basnetsaroj/Batch_distillation_paper/CAD Model/Traditional/Trad photos/Traditional assembled.png

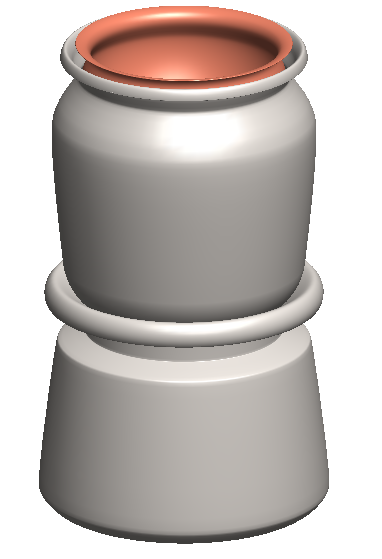
CAD Model/Traditional/Trad photos/Traditional assembled.png
