basnetsaroj/Batch_distillation_paper/CAD Model/CAD/Design Photos/Base container.png

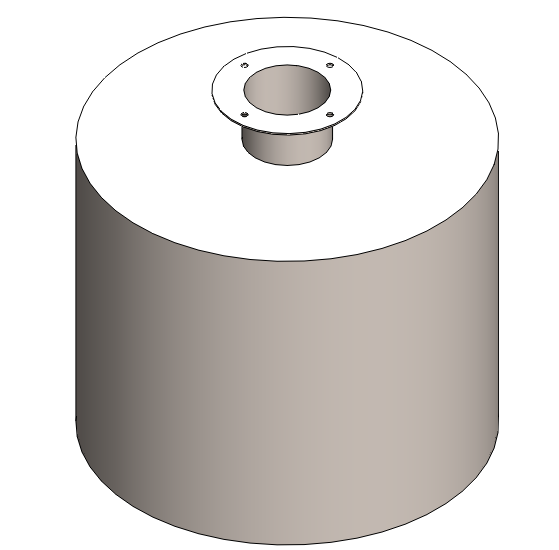
CAD Model/CAD/Design Photos/Base container.png
