basnetsaroj/Batch_distillation_paper/CAD Model/CAD/Design Photos/Column.png

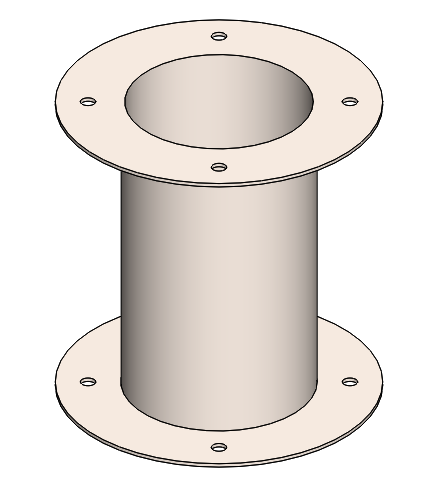
CAD Model/CAD/Design Photos/Column.png
