basnetsaroj/Batch_distillation_paper/CAD Model/CAD/Design Photos/condenser 2.PNG

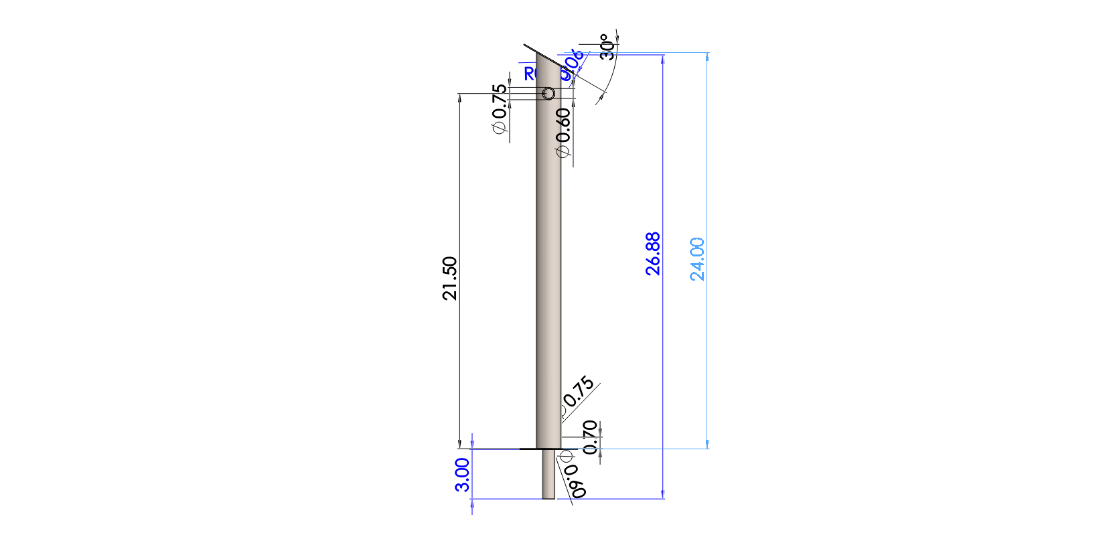
CAD Model/CAD/Design Photos/condenser 2.PNG
