basnetsaroj/Batch_distillation_paper/CAD Model/CAD/Design Photos/Condensor.PNG

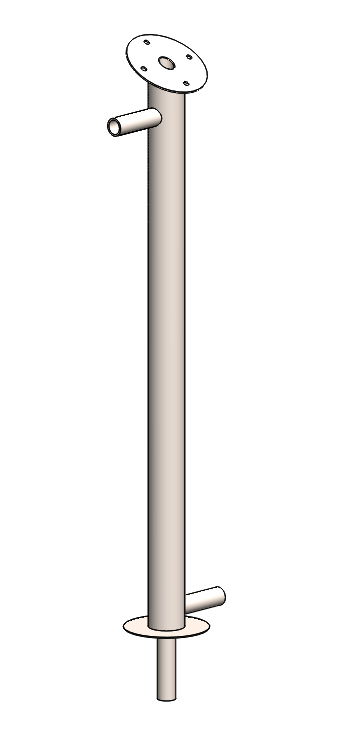
CAD Model/CAD/Design Photos/Condensor.PNG
