basnetsaroj/Batch_distillation_paper/CAD Model/CAD/Design Photos/dc.png

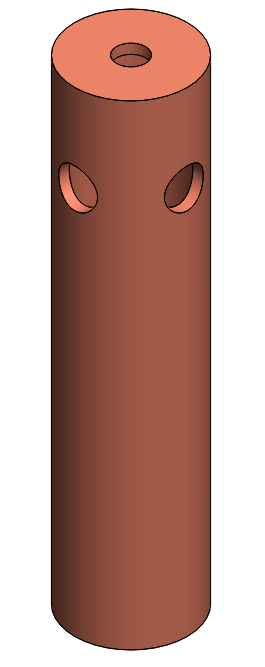
CAD Model/CAD/Design Photos/dc.png
