basnetsaroj/Batch_distillation_paper/CAD Model/CAD/Design Photos/Exploded Section of tray.png

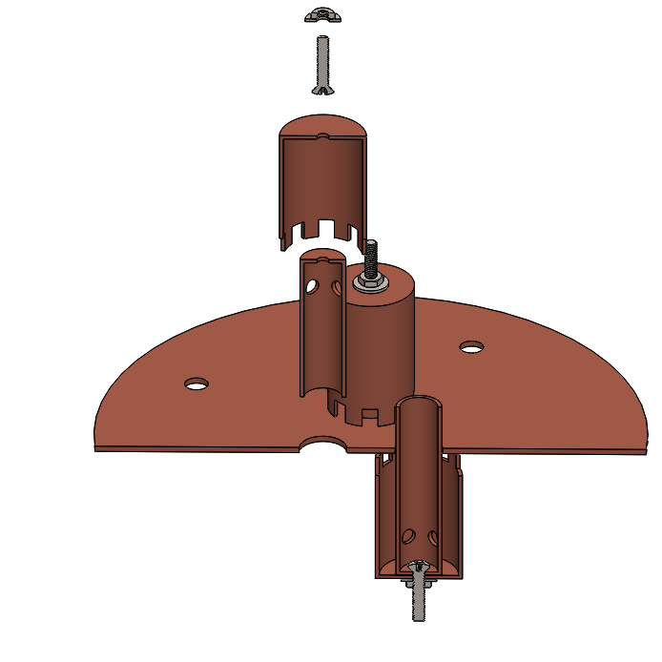
CAD Model/CAD/Design Photos/Exploded Section of tray.png
