basnetsaroj/Batch_distillation_paper/CAD Model/CAD/Design Photos/exploded.png

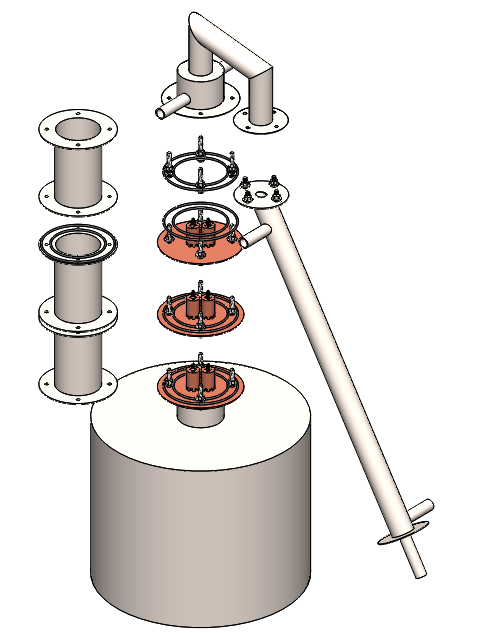
CAD Model/CAD/Design Photos/exploded.png
