basnetsaroj/Batch_distillation_paper/CAD Model/CAD/Design Photos/Gasket.png

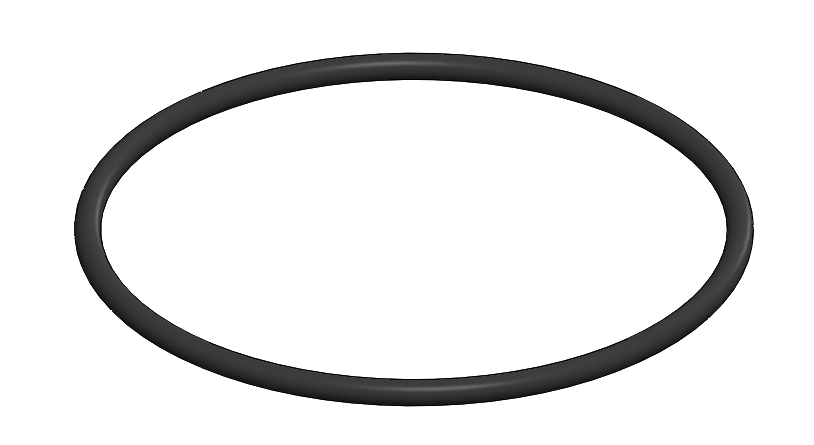
CAD Model/CAD/Design Photos/Gasket.png
