basnetsaroj/Batch_distillation_paper/CAD Model/CAD/Design Photos/Raiser.png

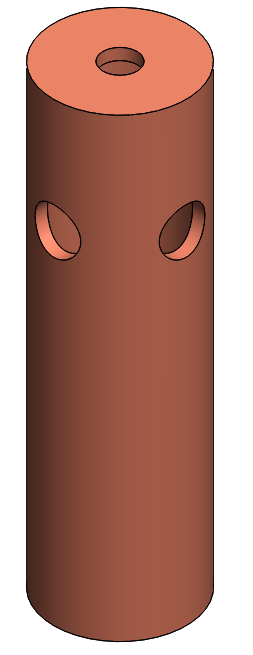
CAD Model/CAD/Design Photos/Raiser.png
