basnetsaroj/Batch_distillation_paper/CAD Model/CAD/Design Photos/reflux Condensor.png

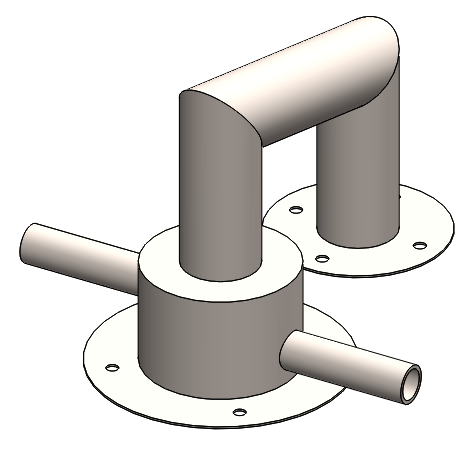
CAD Model/CAD/Design Photos/reflux Condensor.png
