basnetsaroj/Batch_distillation_paper/CAD Model/CAD/Design Photos/s2.png

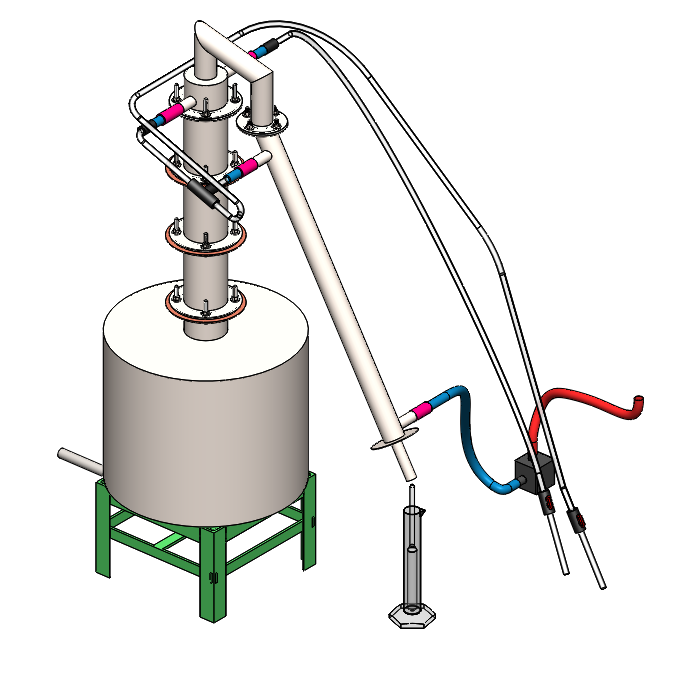
CAD Model/CAD/Design Photos/s2.png
