basnetsaroj/Batch_distillation_paper/CAD Model/CAD/Design Photos/SBase container.png

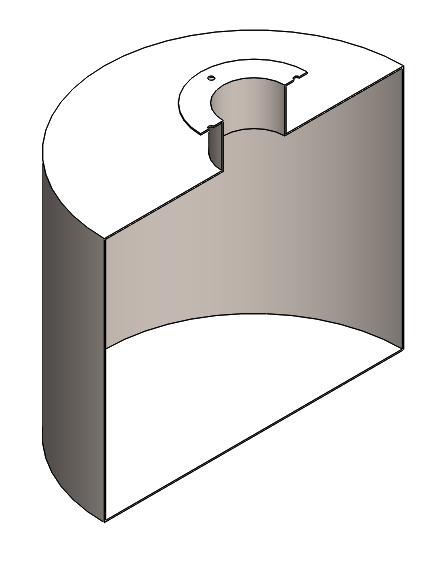
CAD Model/CAD/Design Photos/SBase container.png
