basnetsaroj/Batch_distillation_paper/CAD Model/CAD/Design Photos/SBubble Cap.png

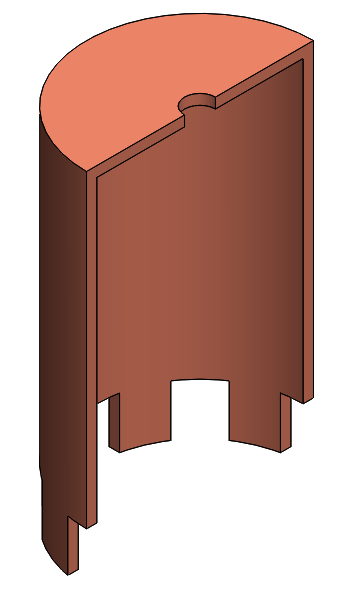
CAD Model/CAD/Design Photos/SBubble Cap.png
