basnetsaroj/Batch_distillation_paper/CAD Model/CAD/Design Photos/Sdc.png

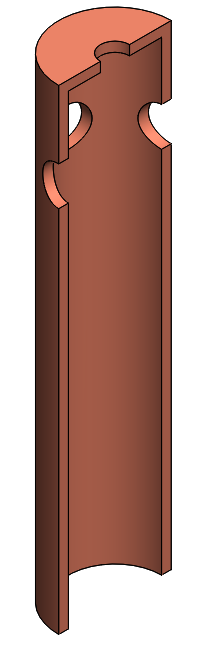
CAD Model/CAD/Design Photos/Sdc.png
