basnetsaroj/Batch_distillation_paper/CAD Model/CAD/Design Photos/Sdowncomer.png

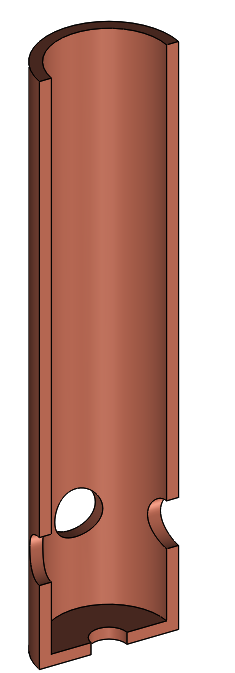
CAD Model/CAD/Design Photos/Sdowncomer.png
