basnetsaroj/Batch_distillation_paper/CAD Model/CAD/Design Photos/SRaiser.png

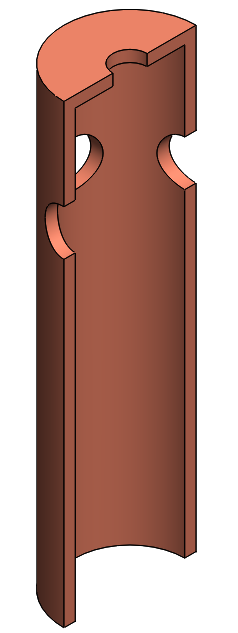
CAD Model/CAD/Design Photos/SRaiser.png
