basnetsaroj/Batch_distillation_paper/CAD Model/CAD/Design Photos/Sreflux Condensor.png

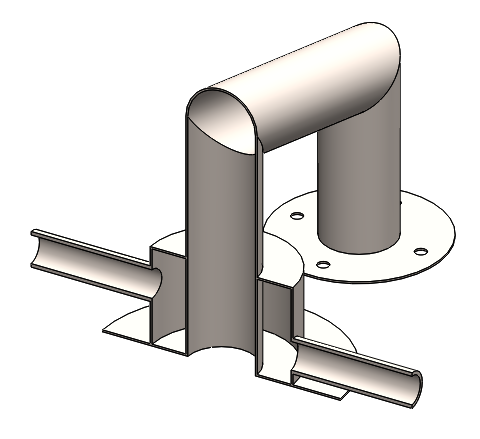
CAD Model/CAD/Design Photos/Sreflux Condensor.png
