basnetsaroj/Batch_distillation_paper/CAD Model/CAD/Design Photos/SStage tray.png

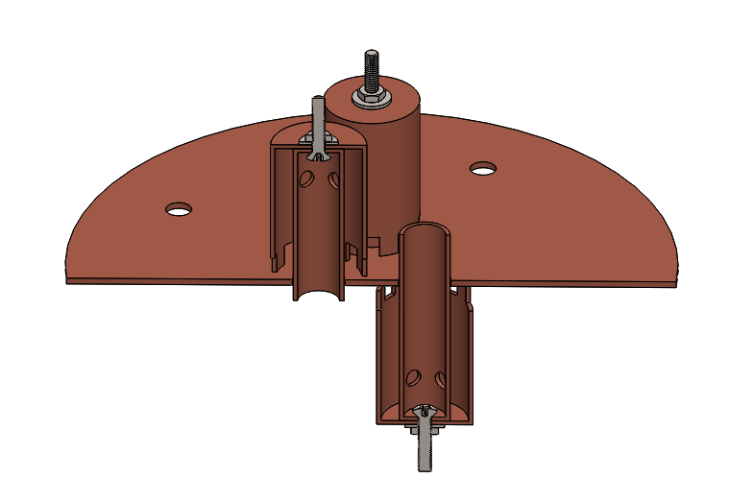
CAD Model/CAD/Design Photos/SStage tray.png
