basnetsaroj/Batch_distillation_paper/CAD Model/CAD/Design Photos/Stage tray.png

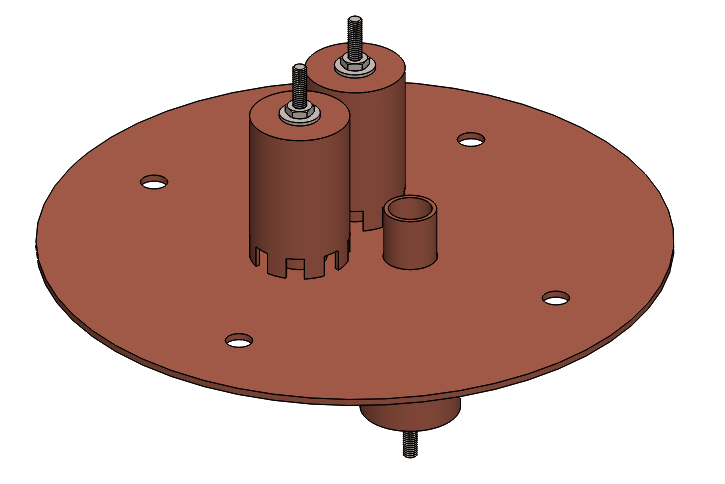
CAD Model/CAD/Design Photos/Stage tray.png
