basnetsaroj/Batch_distillation_paper/CAD Model/CAD/Design Photos/Tray1.png

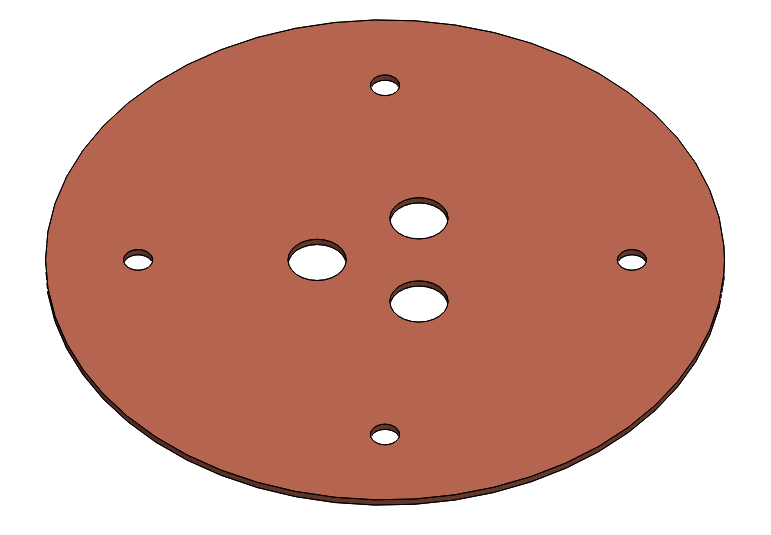
CAD Model/CAD/Design Photos/Tray1.png
