basnetsaroj/Batch_distillation_paper/CAD Model/CAD/Dimension/base new dim.PNG

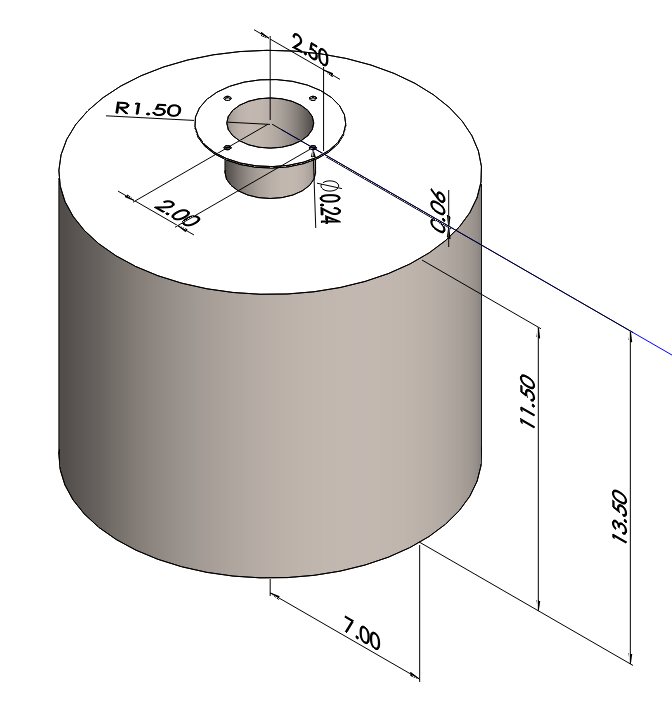
CAD Model/CAD/Dimension/base new dim.PNG
