basnetsaroj/Batch_distillation_paper/CAD Model/CAD/Dimension/bubble cap dim.PNG

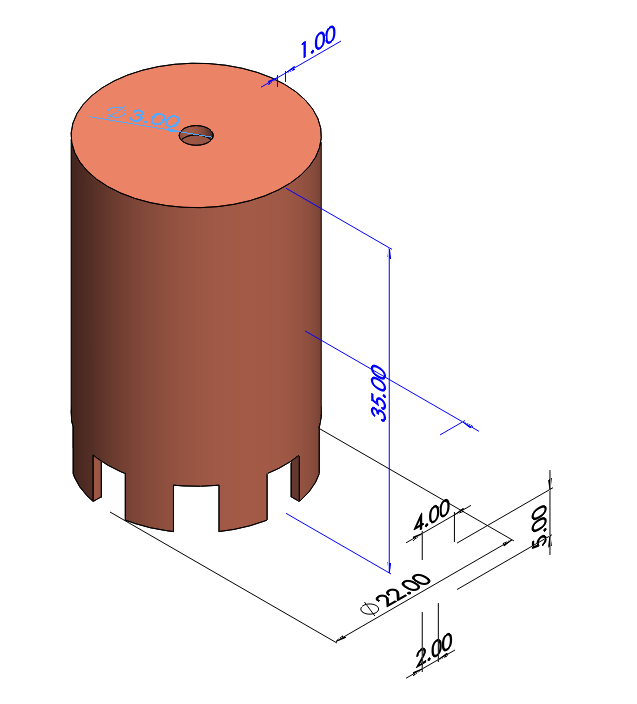
CAD Model/CAD/Dimension/bubble cap dim.PNG
