basnetsaroj/Batch_distillation_paper/CAD Model/CAD/Dimension/column dim.PNG

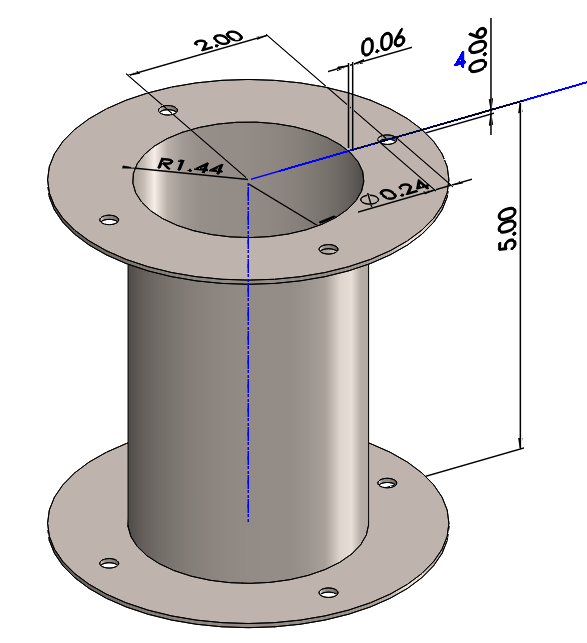
CAD Model/CAD/Dimension/column dim.PNG
