basnetsaroj/Batch_distillation_paper/CAD Model/CAD/Dimension/condenser 2 dim.PNG

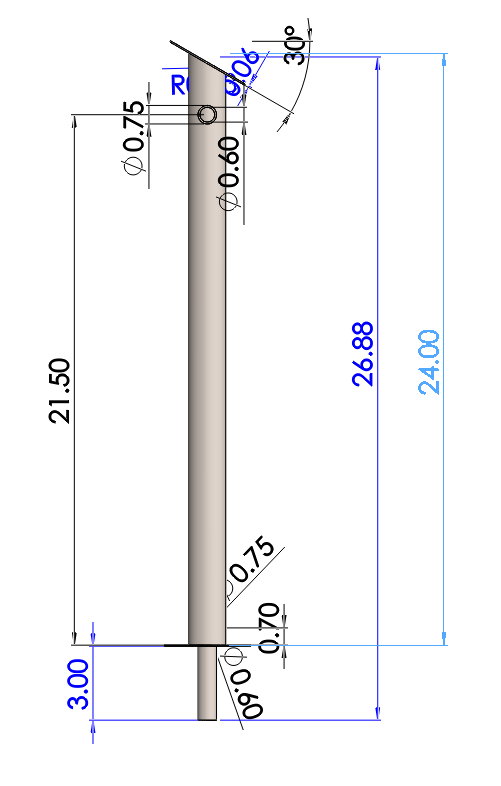
CAD Model/CAD/Dimension/condenser 2 dim.PNG
