basnetsaroj/Batch_distillation_paper/CAD Model/CAD/Dimension/downcomer dim.PNG

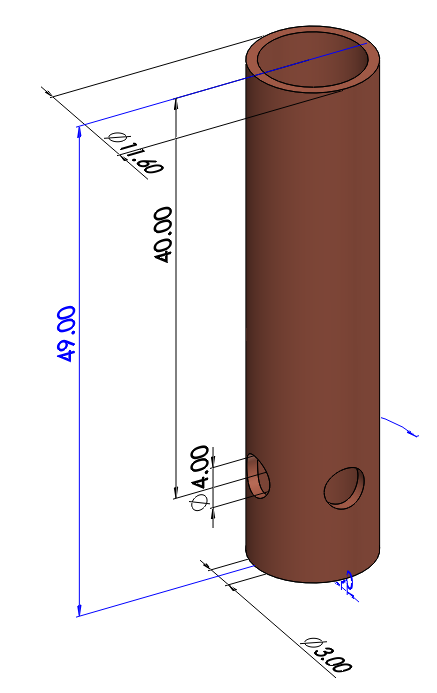
CAD Model/CAD/Dimension/downcomer dim.PNG
