basnetsaroj/Batch_distillation_paper/CAD Model/CAD/Dimension/gasket dim 1.png

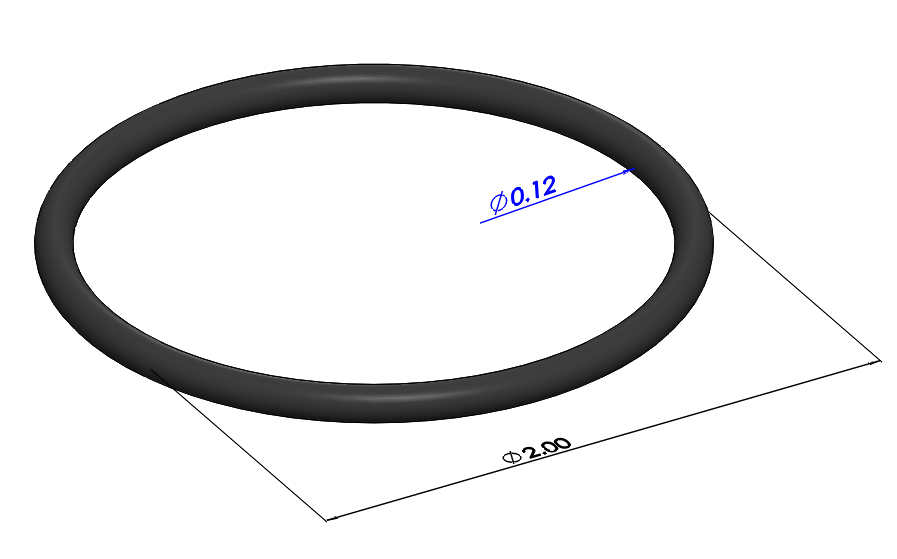
CAD Model/CAD/Dimension/gasket dim 1.png
