basnetsaroj/Batch_distillation_paper/CAD Model/CAD/Dimension/raiser dim.PNG

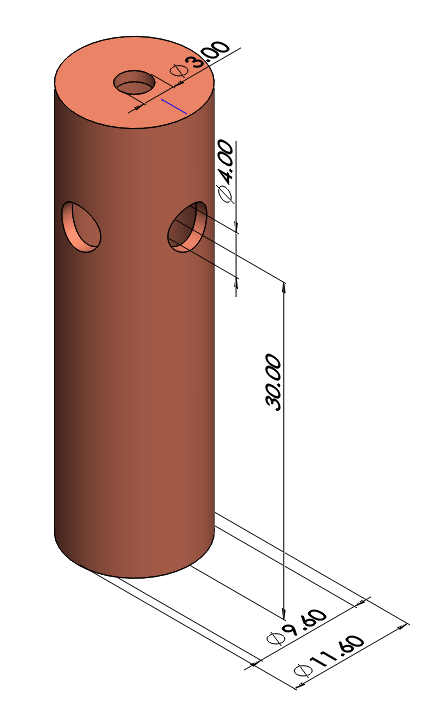
CAD Model/CAD/Dimension/raiser dim.PNG
