basnetsaroj/Batch_distillation_paper/CAD Model/CAD/Dimension/ref cond dim.PNG

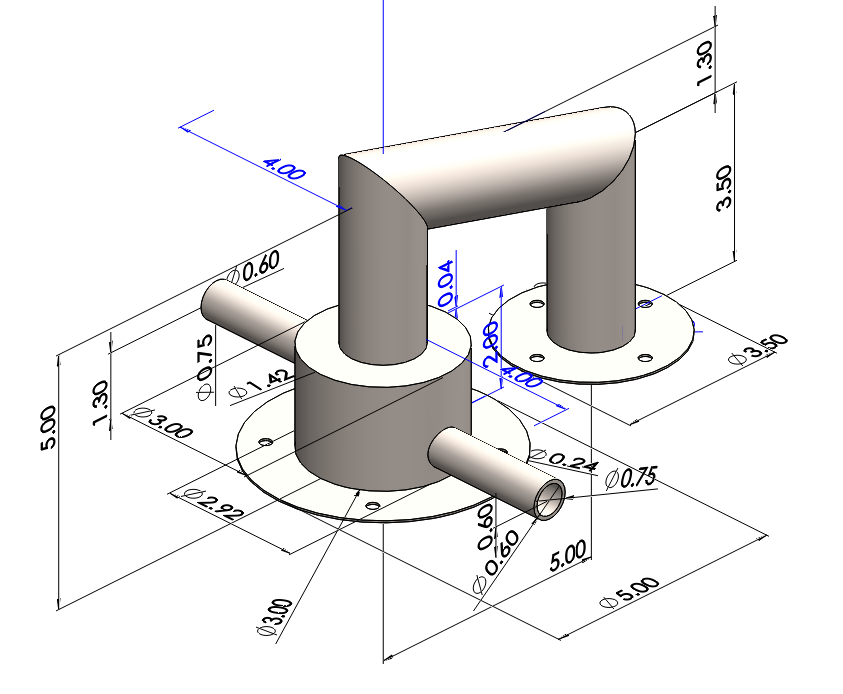
CAD Model/CAD/Dimension/ref cond dim.PNG
