basnetsaroj/Batch_distillation_paper/CAD Model/CAD/Dimension/Tray dim.PNG

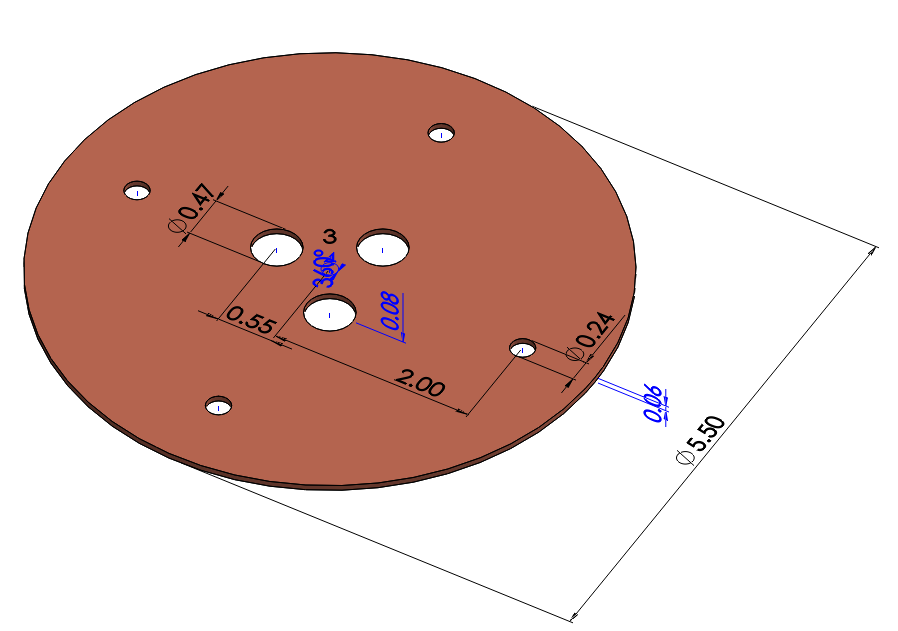
CAD Model/CAD/Dimension/Tray dim.PNG
