basnetsaroj/Batch_distillation_paper/CAD Model/CAD/Dimension/tray plate.png

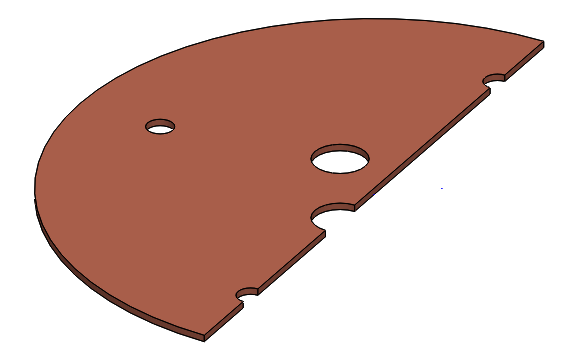
CAD Model/CAD/Dimension/tray plate.png
