basnetsaroj/Batch_distillation_paper/CAD Model/Traditional/p3 cooler.jpg

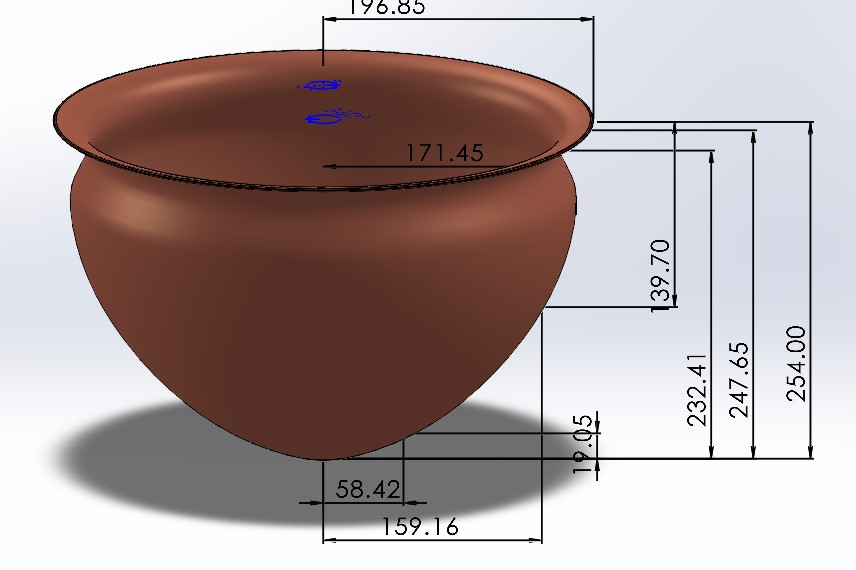
CAD Model/Traditional/p3 cooler.jpg
