basnetsaroj/Batch_distillation_paper/CAD Model/Traditional/p4.0.jpg

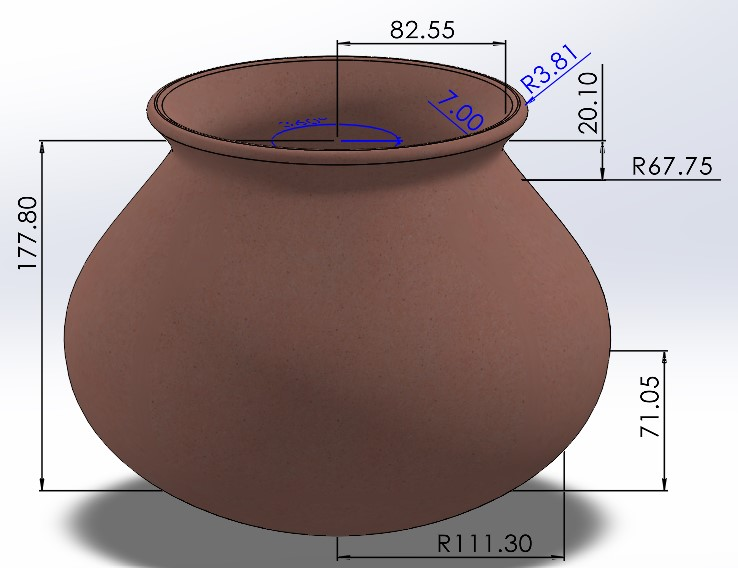
CAD Model/Traditional/p4.0.jpg
