basnetsaroj/Batch_distillation_paper/CAD Model/Traditional/trad base ortho.PNG

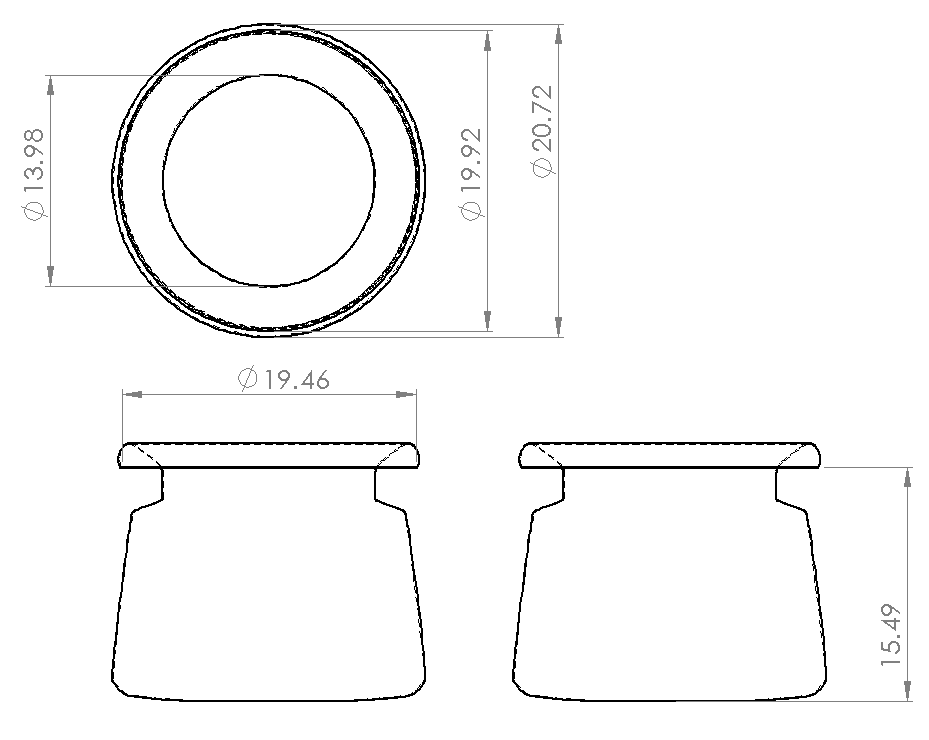
CAD Model/Traditional/trad base ortho.PNG
