basnetsaroj/Batch_distillation_paper/CAD Model/Traditional/trad collector ortho.PNG

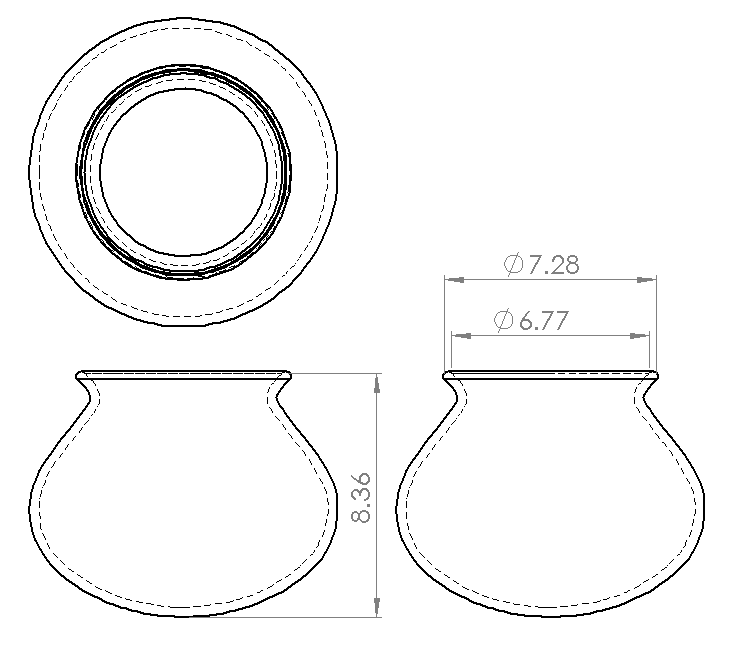
CAD Model/Traditional/trad collector ortho.PNG
