basnetsaroj/Batch_distillation_paper/CAD Model/Traditional/trad column ortho.PNG

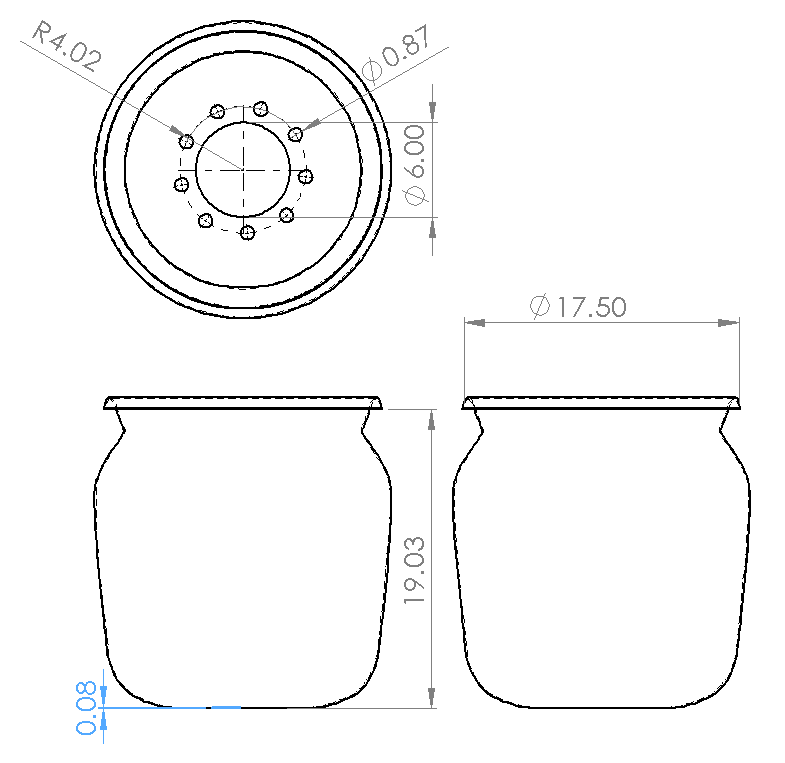
CAD Model/Traditional/trad column ortho.PNG
