basnetsaroj/Batch_distillation_paper/CAD Model/Traditional/trad condenser ortho.PNG

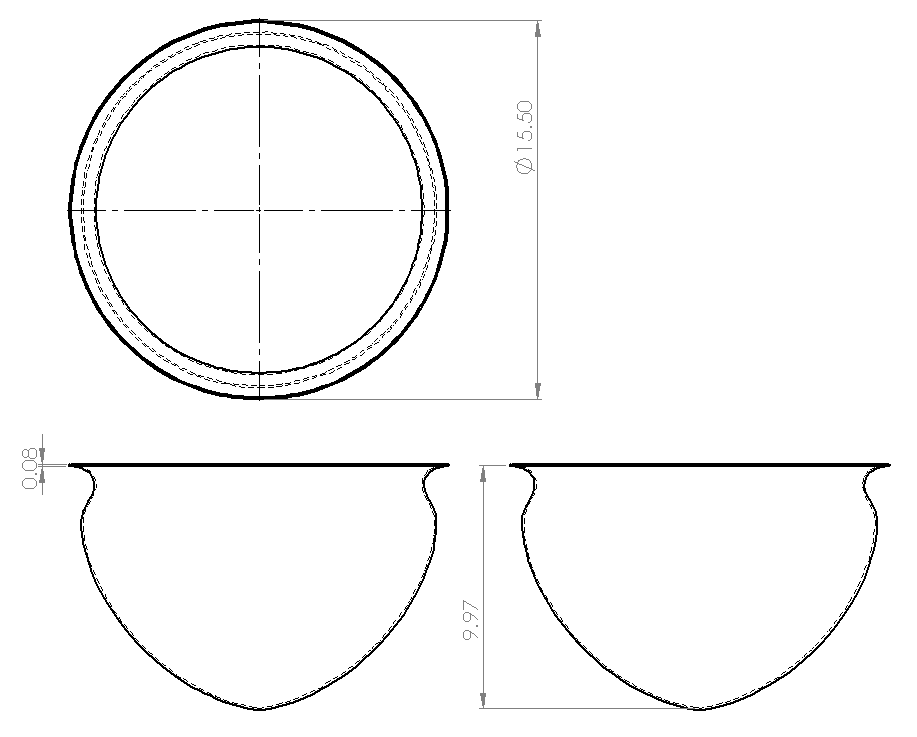
CAD Model/Traditional/trad condenser ortho.PNG
