basnetsaroj/Batch_distillation_paper/CAD Model/Traditional/Trad photos/Bata.png

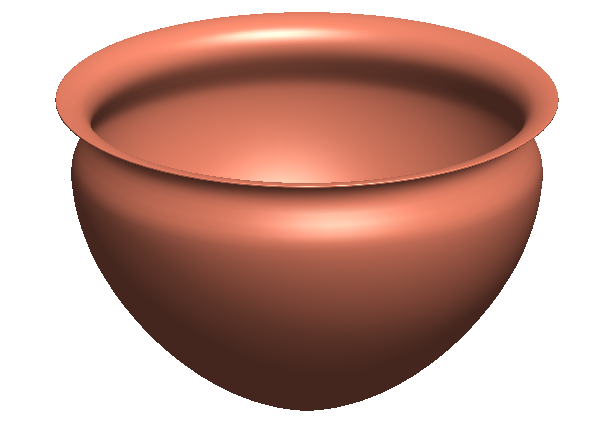
CAD Model/Traditional/Trad photos/Bata.png
