basnetsaroj/Batch_distillation_paper/CAD Model/Traditional/Trad photos/Nani.png

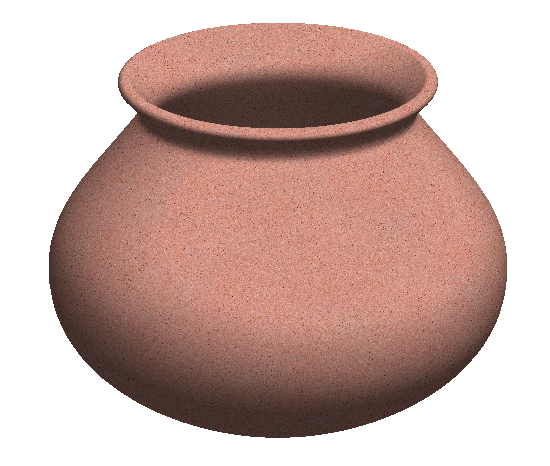
CAD Model/Traditional/Trad photos/Nani.png
