basnetsaroj/Batch_distillation_paper/CAD Model/Traditional/Trad photos/Paini section.png

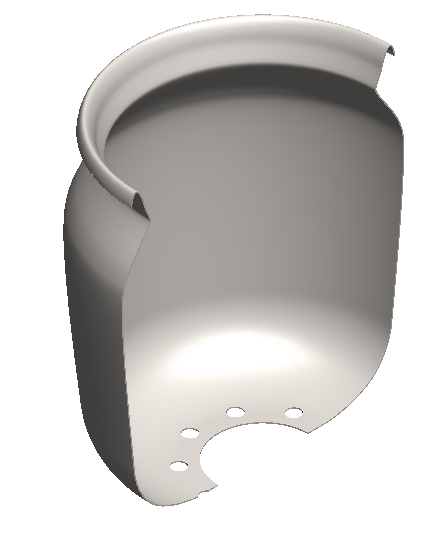
CAD Model/Traditional/Trad photos/Paini section.png
