basnetsaroj/Batch_distillation_paper/CAD Model/Traditional/Trad photos/Paini.png

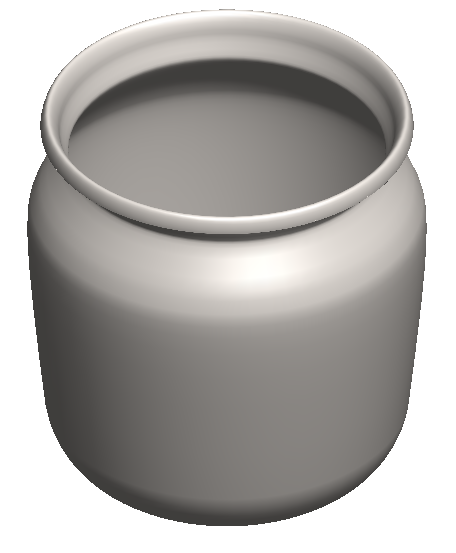
CAD Model/Traditional/Trad photos/Paini.png
