basnetsaroj/Batch_distillation_paper/CAD Model/Traditional/Trad photos/Phonsi section.png

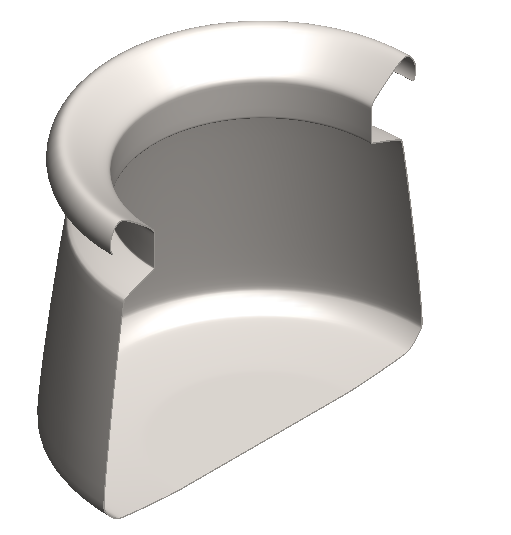
CAD Model/Traditional/Trad photos/Phonsi section.png
