basnetsaroj/Batch_distillation_paper/CAD Model/Traditional/Trad photos/Phonsi.png

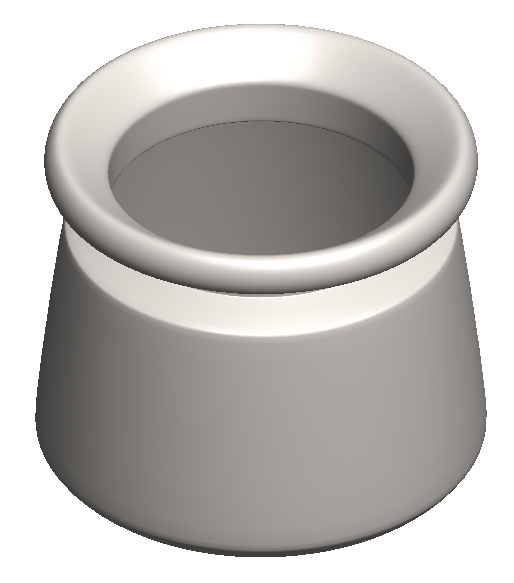
CAD Model/Traditional/Trad photos/Phonsi.png
