basnetsaroj/Batch_distillation_paper/CAD Model/CAD/Final assembly 3.SLDASM

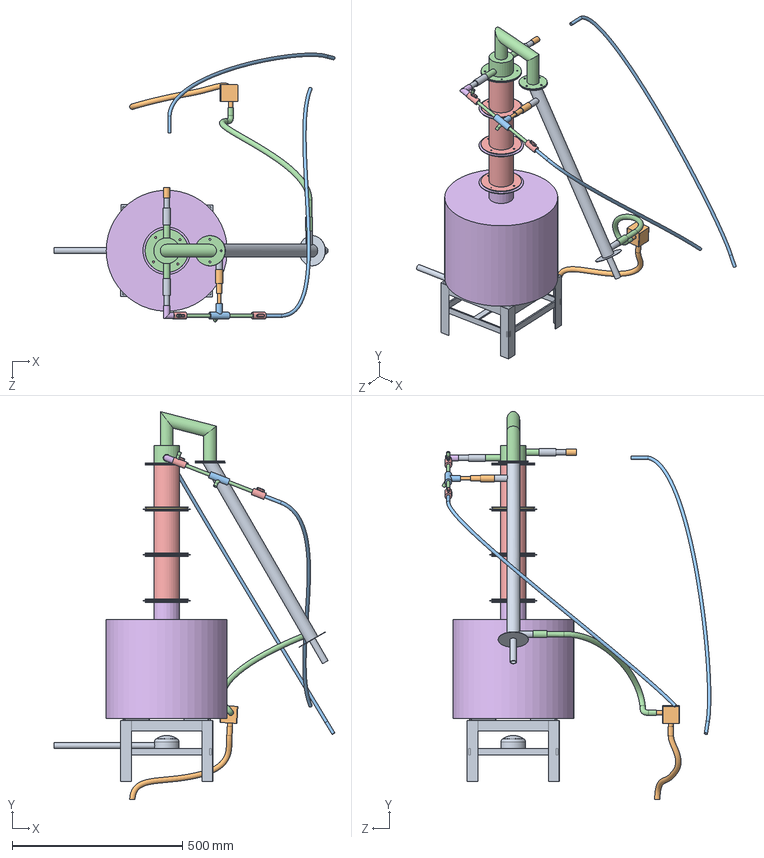
[picture p70: CAD file, 2026-08-13]
CAD Model/CAD/Final assembly 3.SLDASM
825.1 x 1139.8 x 789.6 mm
base new
column x 3
in pipe
out pipe
water motor
condenser 2
gasket 2 x 7
gasket 3 x 7
Tray x 3
internal x 6
curve top
T pipe
connection
connection 2 x 2
gasket condenser
gasket condenser 2nd
L connector
Ball valve x 2
connectpipe x 2
bypass out pipe
connector
stove
