basnetsaroj/Batch_distillation_paper/CAD Model/CAD/Final assembly 2.SLDASM

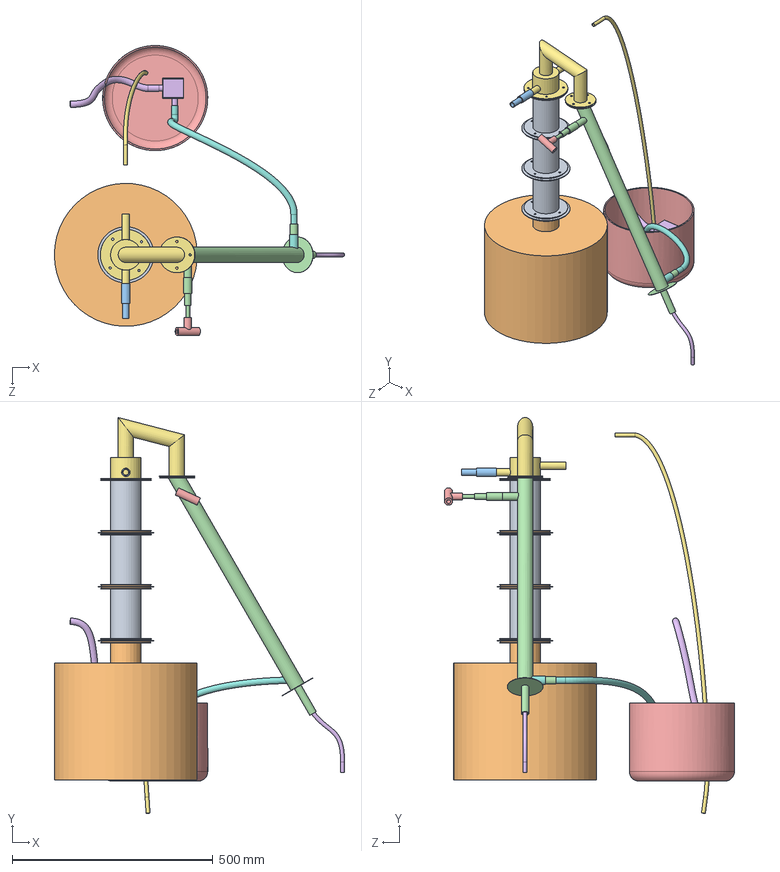
[picture p71: CAD file, 2026-08-13]
CAD Model/CAD/Final assembly 2.SLDASM
722.1 x 985.3 x 721.6 mm
base new
column x 3
in pipe
out pipe
water motor
coolerwater
condenser 2
gasket 2 x 7
gasket 3 x 7
Tray x 3
internal x 6
curve top
Collection pipe
T pipe
connection
connection 2
gasket condenser
gasket condenser 2nd
