basnetsaroj/Batch_distillation_paper/CAD Model/CAD/Final assembly 1.SLDASM

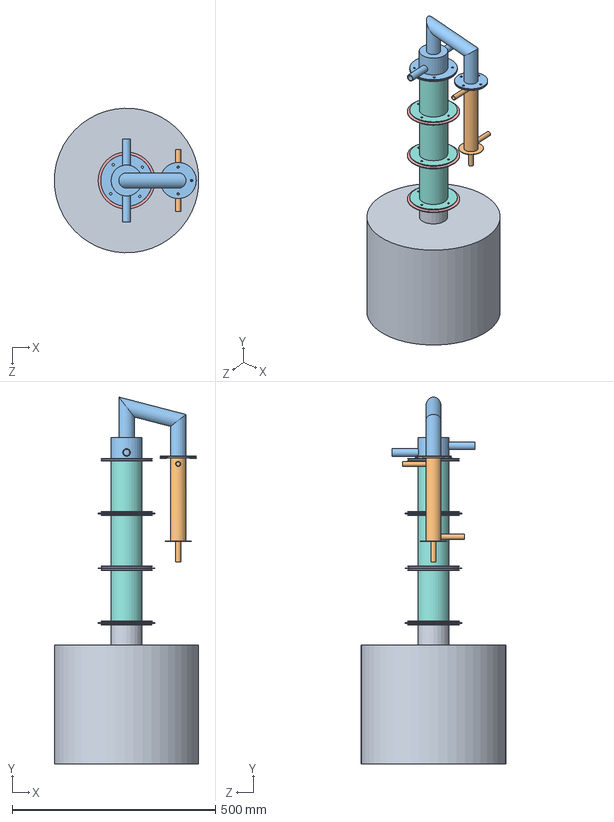
[picture p72: CAD file, 2026-08-13]
CAD Model/CAD/Final assembly 1.SLDASM
355.2 x 902.5 x 355.4 mm
base new
column x 3
gasket 2 x 7
gasket 3 x 7
Tray x 3
internal x 6
curve top
condenser 1
gasket condenser
