basnetsaroj/Batch_distillation_paper/CAD Model/CAD/gasket 2.SLDPRT

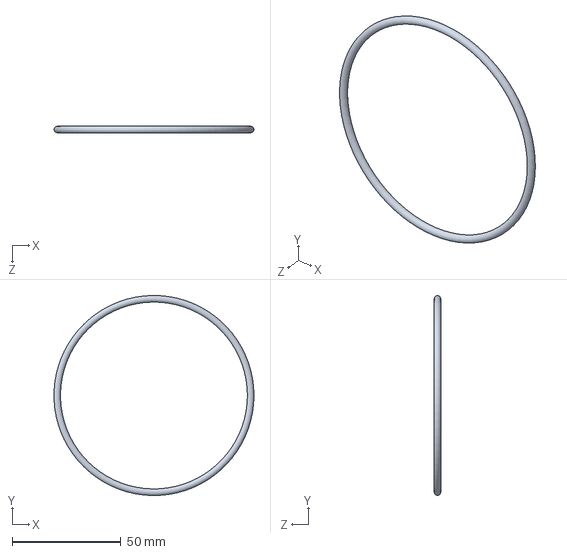
[picture p83: CAD file, 2026-08-13]
CAD Model/CAD/gasket 2.SLDPRT
91.9 x 91.9 x 3.05 mm
