basnetsaroj/Batch_distillation_paper/CAD Model/CAD/tube.SLDPRT

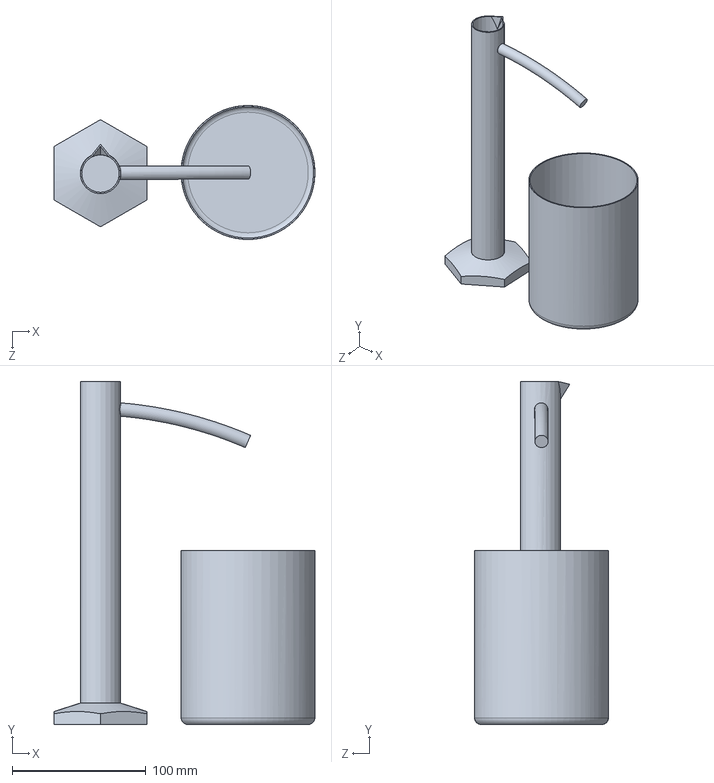
[picture p84: CAD file, 2026-08-13]
CAD Model/CAD/tube.SLDPRT
194.7 x 256.0 x 100.0 mm
