basnetsaroj/Batch_distillation_paper/CAD Model/CAD/concentrationtest.SLDPRT

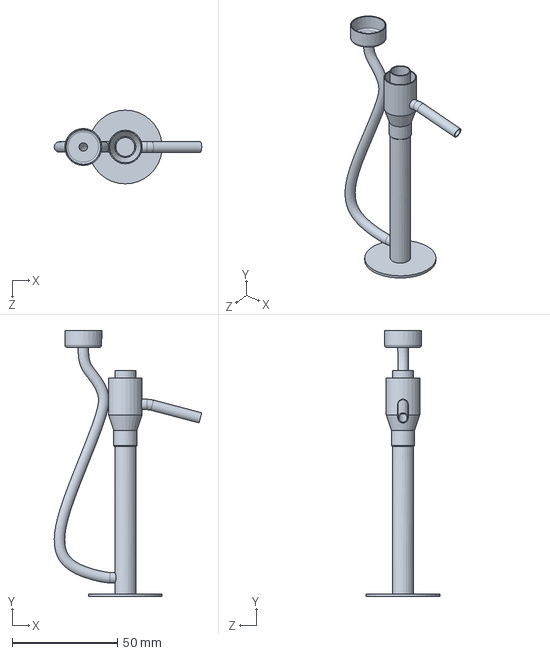
[picture p85: CAD file, 2026-08-13]
CAD Model/CAD/concentrationtest.SLDPRT
70.1 x 126.3 x 35.0 mm
