basnetsaroj/Batch_distillation_paper/CAD Model/CAD/Collection pipe.SLDPRT

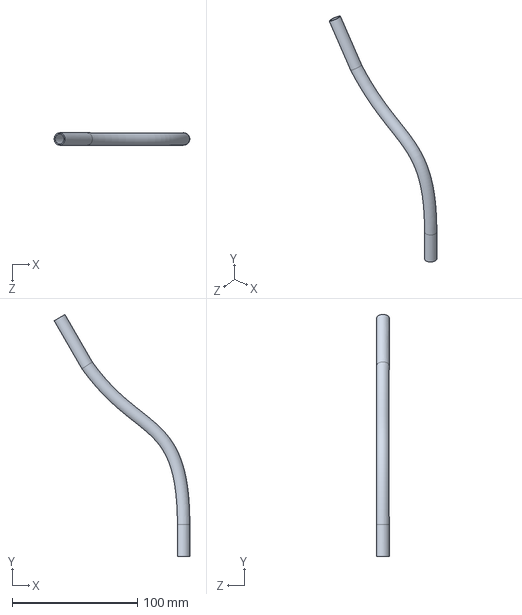
[picture p86: CAD file, 2026-08-13]
CAD Model/CAD/Collection pipe.SLDPRT
108.3 x 193.0 x 10.0 mm
