basnetsaroj/Batch_distillation_paper/CAD Model/CAD/internal.SLDPRT

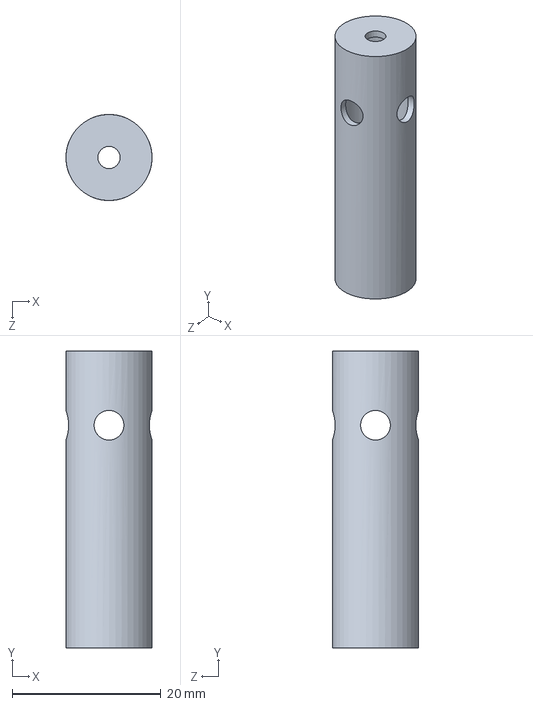
[picture p87: CAD file, 2026-08-13]
CAD Model/CAD/internal.SLDPRT
11.6 x 40.0 x 11.6 mm
