basnetsaroj/Batch_distillation_paper/CAD Model/CAD/bubble cap.SLDPRT

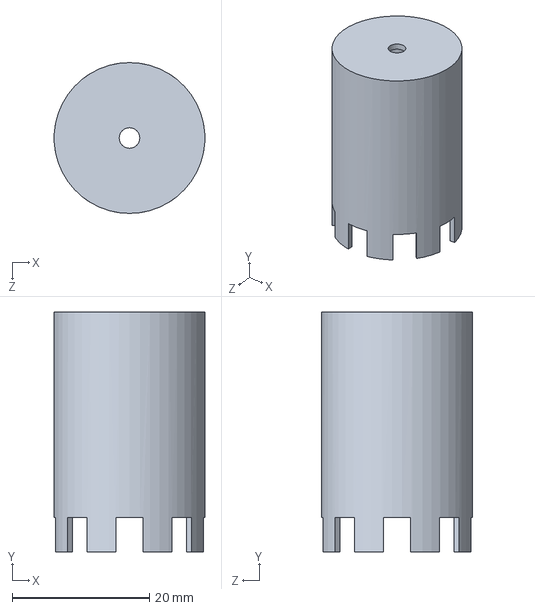
[picture p88: CAD file, 2026-08-13]
CAD Model/CAD/bubble cap.SLDPRT
21.9 x 35.0 x 22.0 mm
