basnetsaroj/Batch_distillation_paper/CAD Model/CAD/in pipe 2.SLDPRT

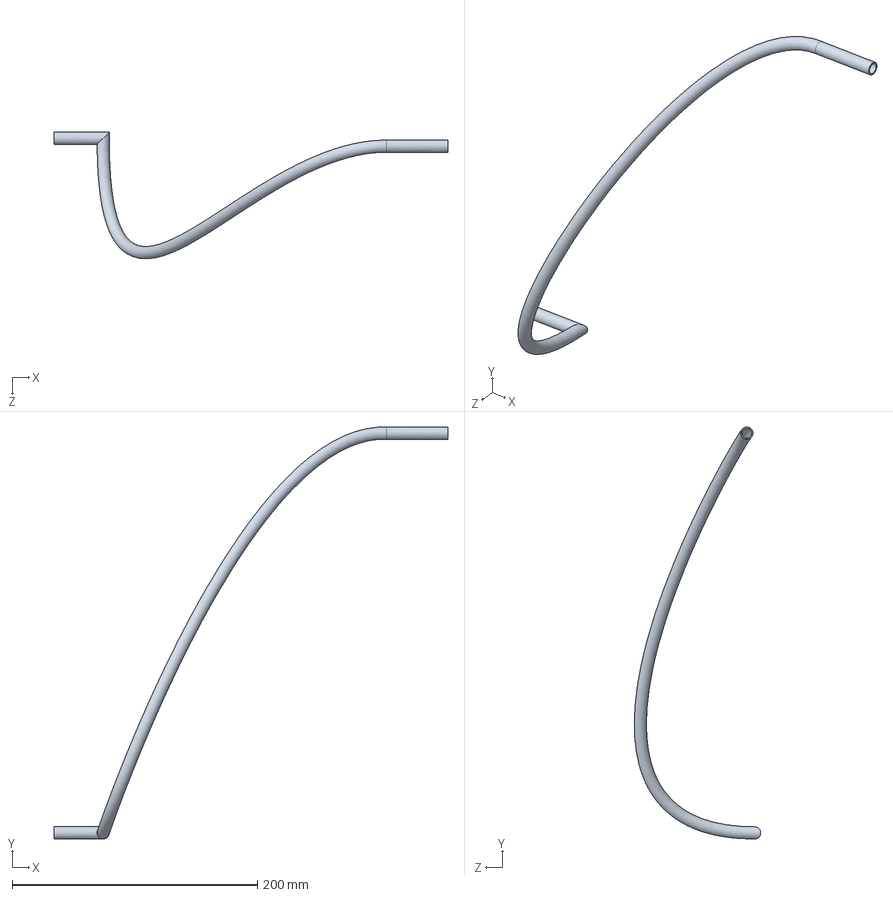
[picture p89: CAD file, 2026-08-13]
CAD Model/CAD/in pipe 2.SLDPRT
321.3 x 336.3 x 103.3 mm
