basnetsaroj/Batch_distillation_paper/CAD Model/CAD/stove.SLDPRT

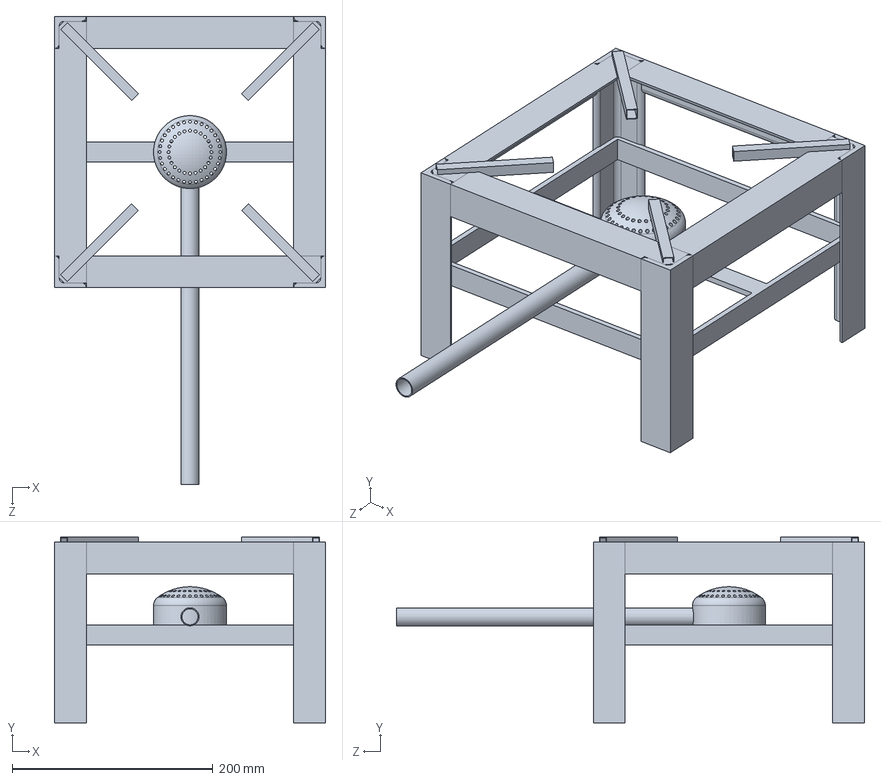
[picture p90: CAD file, 2026-08-13]
CAD Model/CAD/stove.SLDPRT
270.0 x 184.8 x 466.0 mm
