basnetsaroj/Batch_distillation_paper/CAD Model/CAD/water motor.SLDPRT

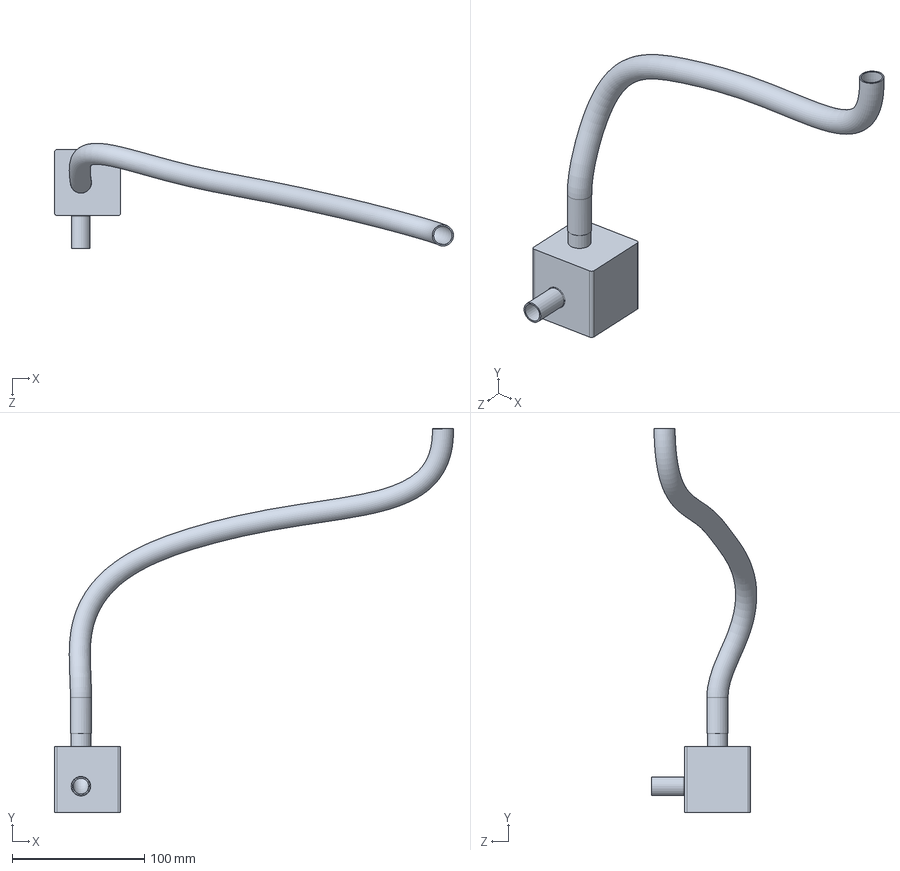
[picture p91: CAD file, 2026-08-13]
CAD Model/CAD/water motor.SLDPRT
301.7 x 290.6 x 79.7 mm
