basnetsaroj/Batch_distillation_paper/CAD Model/CAD/coolerwater.SLDPRT

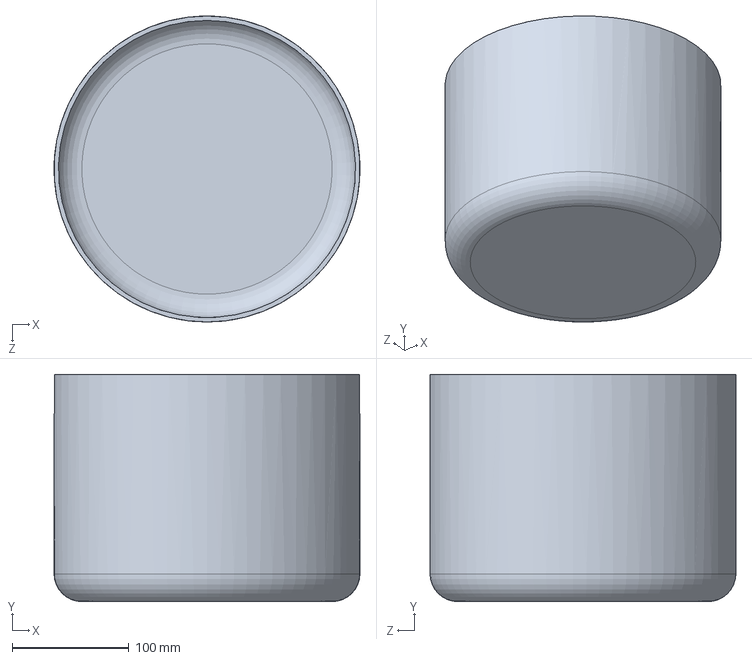
[picture p92: CAD file, 2026-08-13]
CAD Model/CAD/coolerwater.SLDPRT
261.6 x 194.3 x 261.6 mm
