basnetsaroj/Batch_distillation_paper/CAD Model/CAD/column.SLDPRT

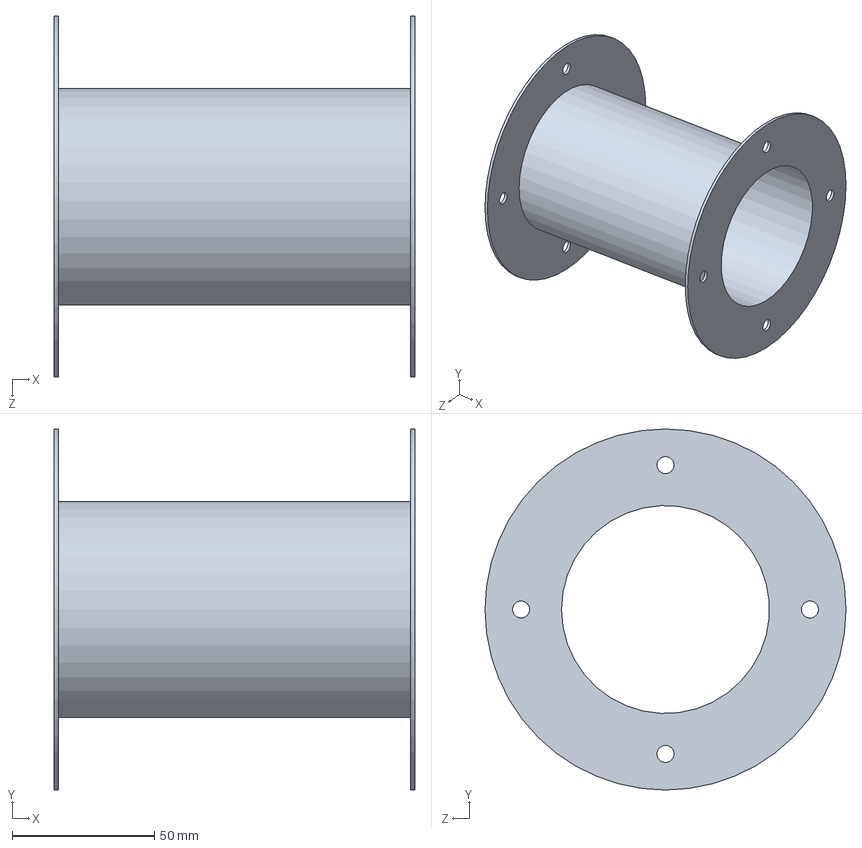
[picture p93: CAD file, 2026-08-13]
CAD Model/CAD/column.SLDPRT
127.0 x 127.0 x 127.0 mm
