basnetsaroj/Batch_distillation_paper/CAD Model/CAD/connector.SLDPRT

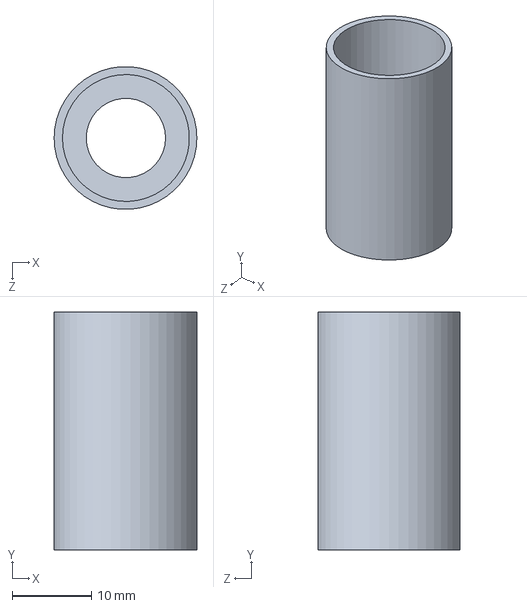
[picture p94: CAD file, 2026-08-13]
CAD Model/CAD/connector.SLDPRT
18.0 x 30.0 x 18.0 mm
