basnetsaroj/Batch_distillation_paper/CAD Model/CAD/connection.SLDPRT

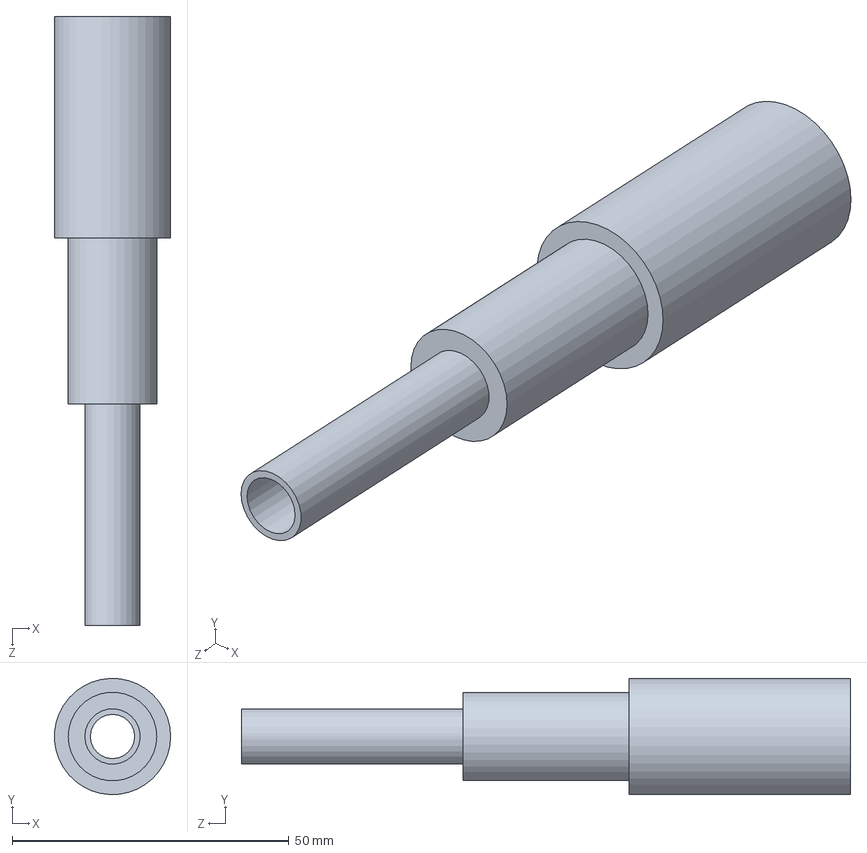
[picture p95: CAD file, 2026-08-13]
CAD Model/CAD/connection.SLDPRT
21.0 x 21.0 x 110.0 mm
