basnetsaroj/Batch_distillation_paper/CAD Model/CAD/Tray.SLDPRT

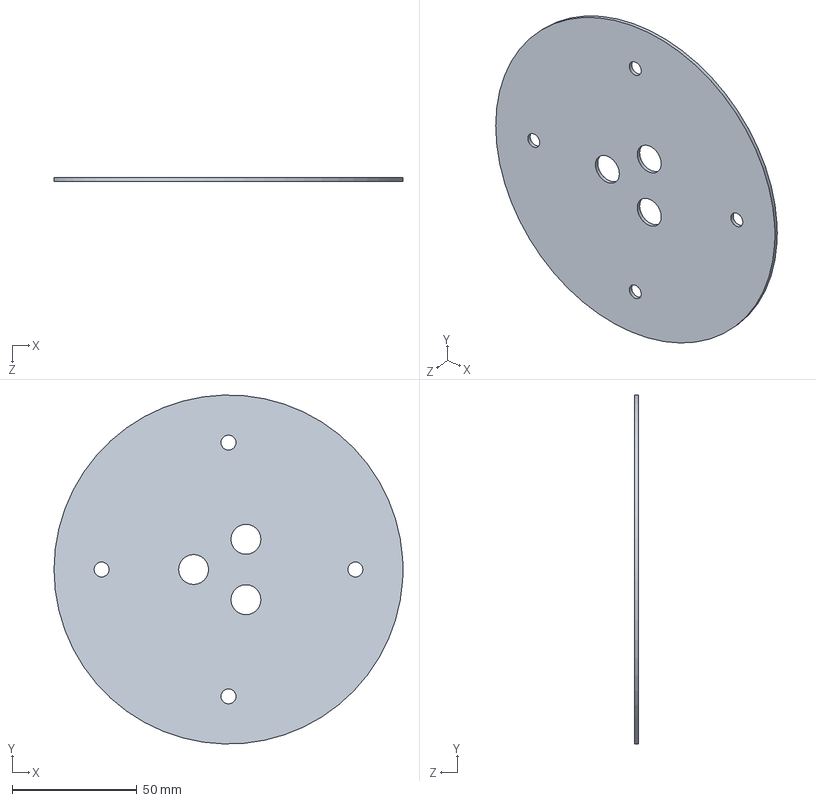
[picture p96: CAD file, 2026-08-13]
CAD Model/CAD/Tray.SLDPRT
139.7 x 139.6 x 1.52 mm
