basnetsaroj/Batch_distillation_paper/CAD Model/CAD/alcoholmeter.SLDPRT

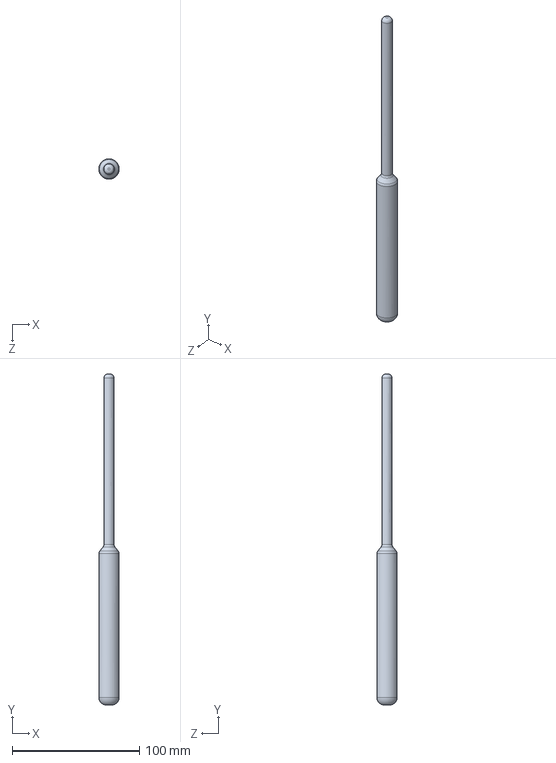
[picture p97: CAD file, 2026-08-13]
CAD Model/CAD/alcoholmeter.SLDPRT
16.0 x 260.0 x 16.0 mm
