basnetsaroj/Batch_distillation_paper/CAD Model/CAD/out pipe.SLDPRT

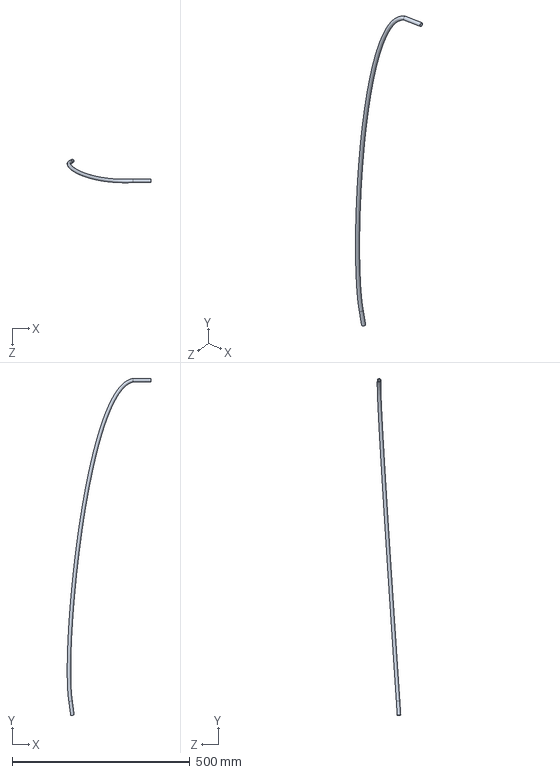
[picture p98: CAD file, 2026-08-13]
CAD Model/CAD/out pipe.SLDPRT
234.8 x 946.9 x 66.2 mm
