basnetsaroj/Batch_distillation_paper/CAD Model/CAD/condenser 2.SLDPRT

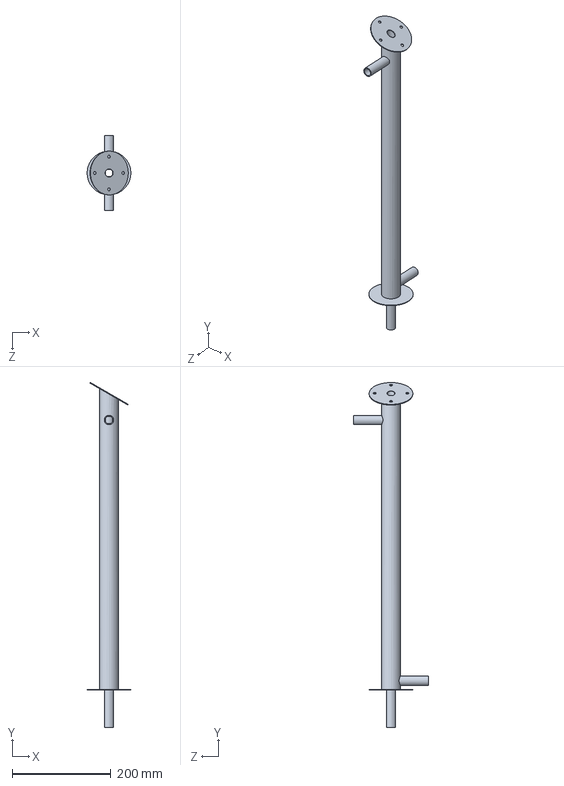
[picture p99: CAD file, 2026-08-13]
CAD Model/CAD/condenser 2.SLDPRT
88.8 x 699.4 x 152.4 mm
