basnetsaroj/Batch_distillation_paper/CAD Model/CAD/curve top.SLDPRT

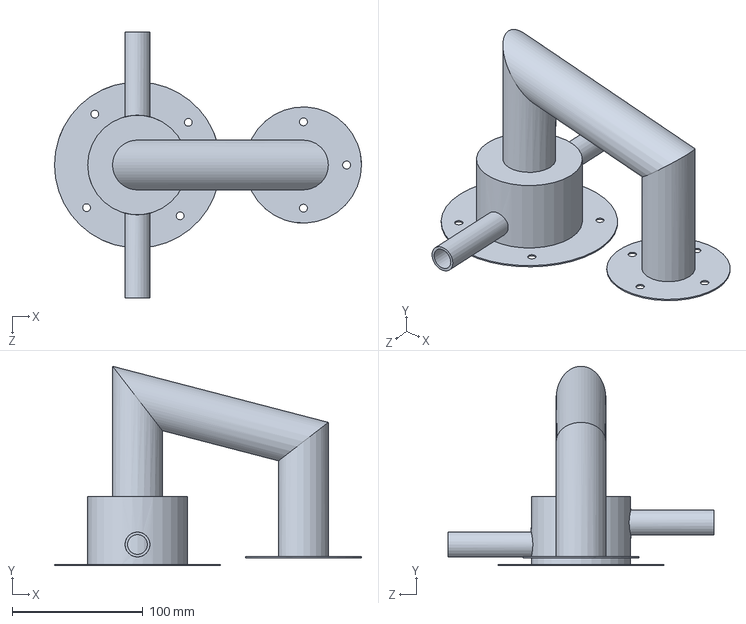
[picture p100: CAD file, 2026-08-13]
CAD Model/CAD/curve top.SLDPRT
235.0 x 152.7 x 203.2 mm
