basnetsaroj/Batch_distillation_paper/CAD Model/CAD/condenser 1.SLDPRT

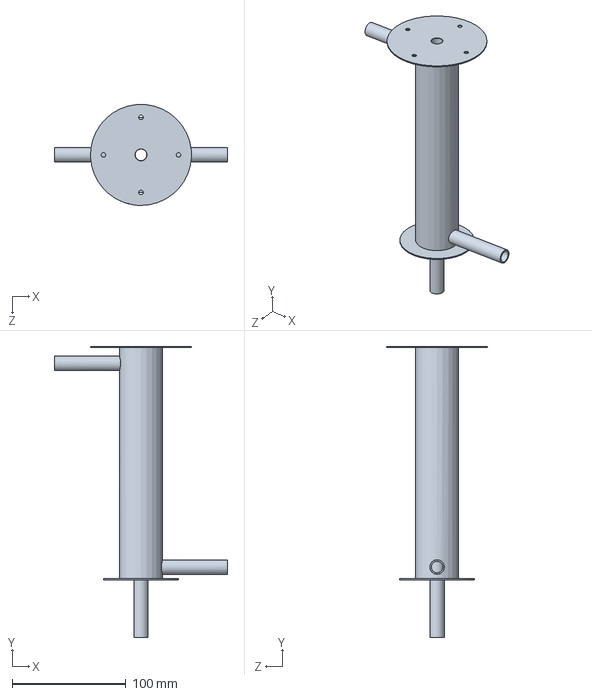
[picture p101: CAD file, 2026-08-13]
CAD Model/CAD/condenser 1.SLDPRT
152.4 x 256.0 x 88.7 mm
