basnetsaroj/Batch_distillation_paper/CAD Model/CAD/T pipe.SLDPRT

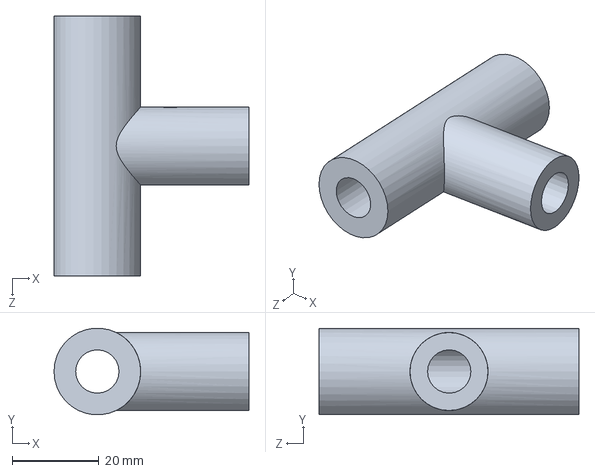
[picture p102: CAD file, 2026-08-13]
CAD Model/CAD/T pipe.SLDPRT
45.0 x 19.9 x 60.0 mm
