basnetsaroj/Batch_distillation_paper/CAD Model/CAD/base new.SLDPRT

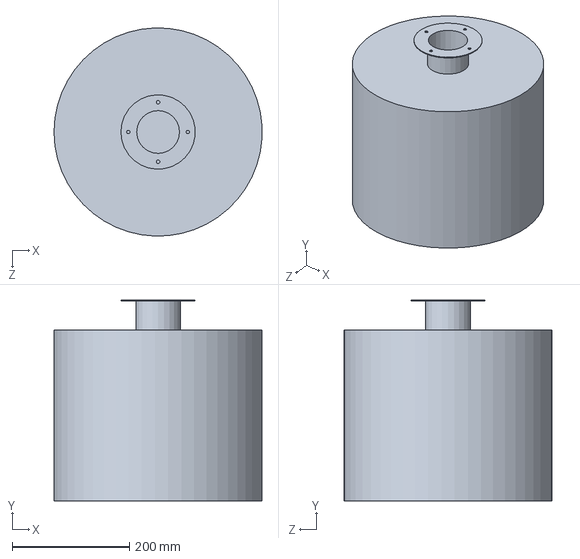
[picture p103: CAD file, 2026-08-13]
CAD Model/CAD/base new.SLDPRT
355.2 x 342.9 x 355.4 mm
