basnetsaroj/Batch_distillation_paper/CAD Model/CAD/pipe 2.SLDPRT

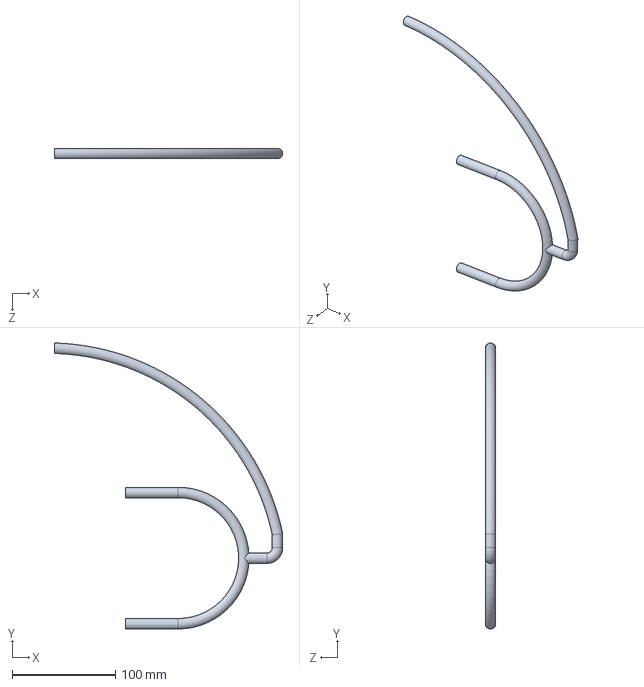
[picture p104: CAD file, 2026-08-13]
CAD Model/CAD/pipe 2.SLDPRT
221.1 x 276.8 x 10.2 mm
