basnetsaroj/Batch_distillation_paper/CAD Model/CAD/bypass out pipe.SLDPRT

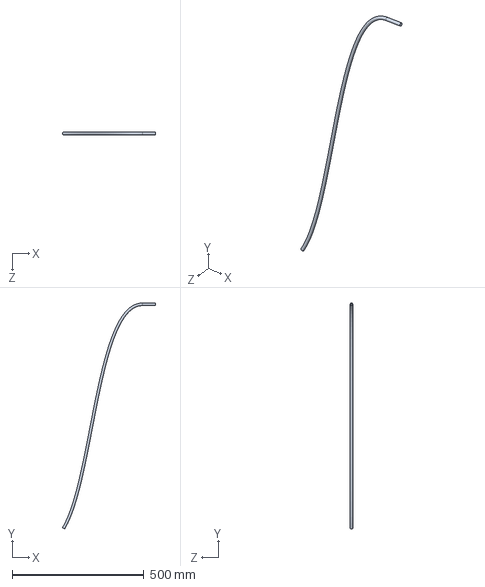
[picture p105: CAD file, 2026-08-13]
CAD Model/CAD/bypass out pipe.SLDPRT
353.0 x 856.5 x 10.0 mm
