basnetsaroj/Batch_distillation_paper/CAD Model/CAD/gasket condenser.SLDPRT

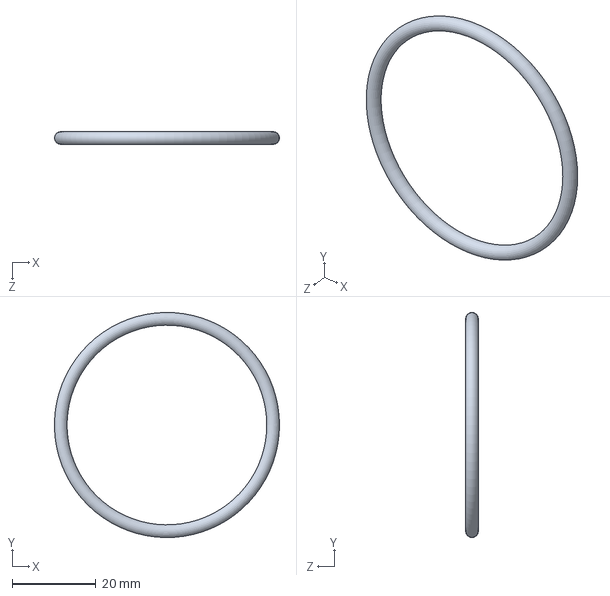
[picture p106: CAD file, 2026-08-13]
CAD Model/CAD/gasket condenser.SLDPRT
53.8 x 53.8 x 3.05 mm
