basnetsaroj/Batch_distillation_paper/CAD Model/CAD/in pipe.SLDPRT

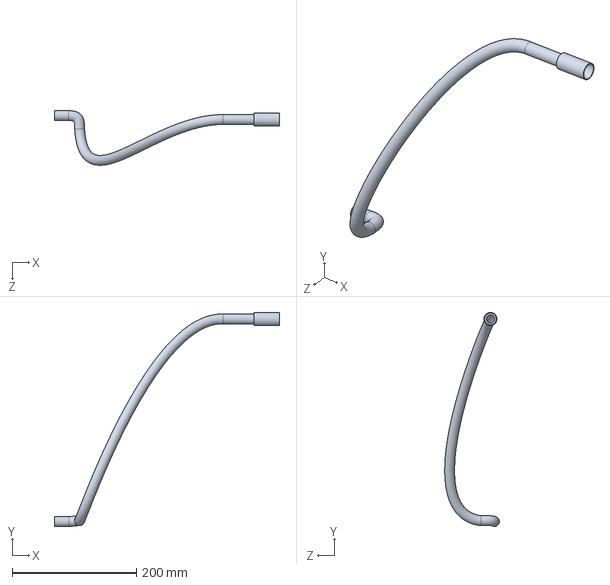
[picture p107: CAD file, 2026-08-13]
CAD Model/CAD/in pipe.SLDPRT
362.3 x 344.7 x 88.1 mm
