basnetsaroj/Batch_distillation_paper/CAD Model/CAD/Ball valve.SLDPRT

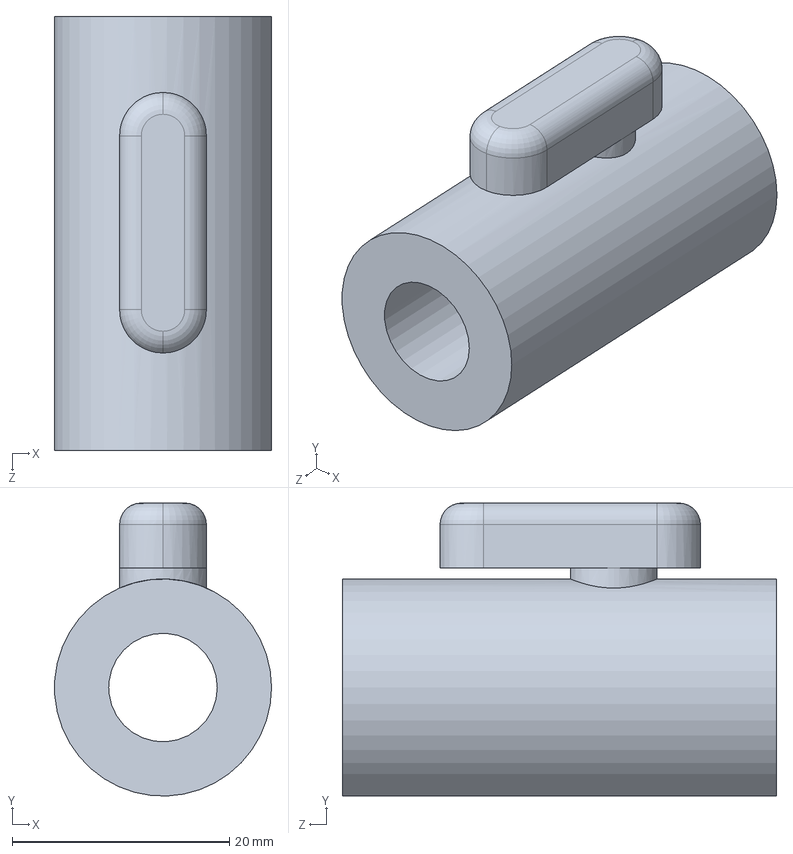
[picture p108: CAD file, 2026-08-13]
CAD Model/CAD/Ball valve.SLDPRT
20.0 x 27.0 x 40.0 mm
