basnetsaroj/Batch_distillation_paper/CAD Model/CAD/gasket condenser 2nd.SLDPRT

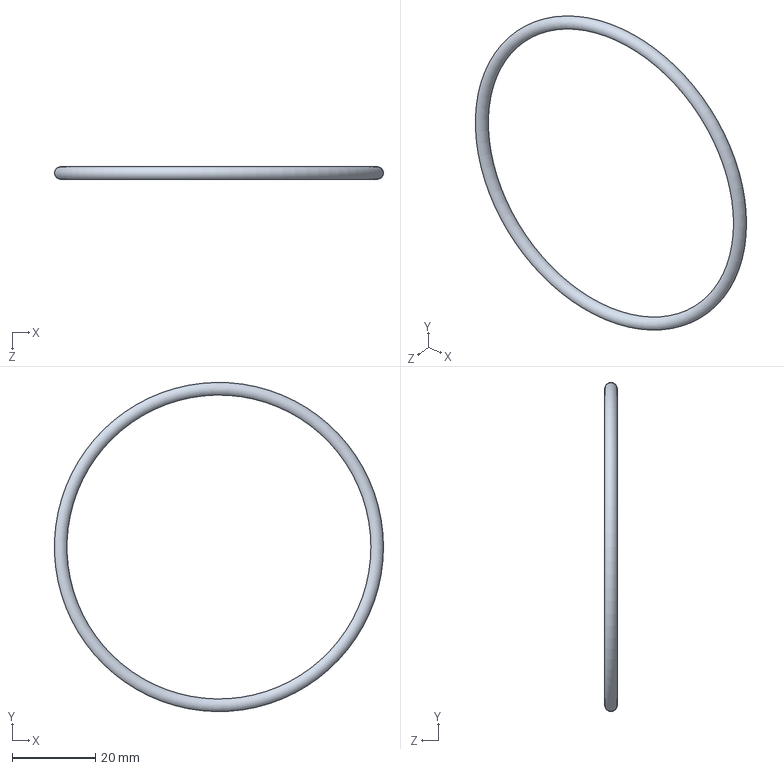
[picture p109: CAD file, 2026-08-13]
CAD Model/CAD/gasket condenser 2nd.SLDPRT
79.2 x 79.2 x 3.05 mm
