basnetsaroj/Batch_distillation_paper/CAD Model/CAD/L connector.SLDPRT

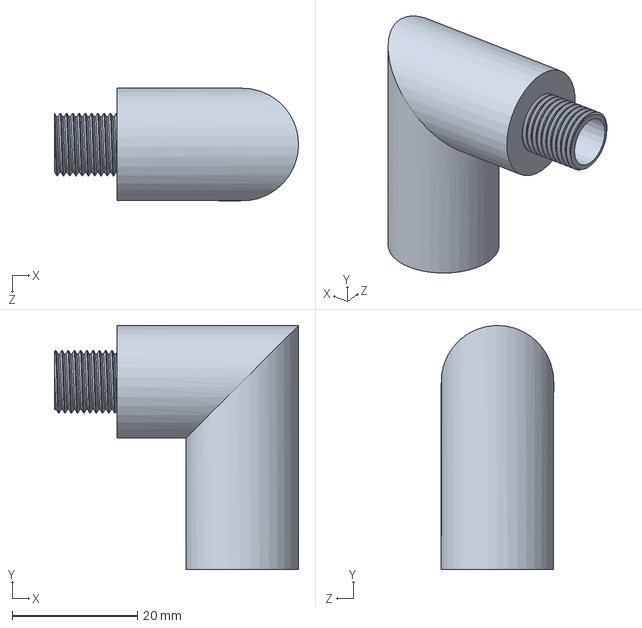
[picture p110: CAD file, 2026-08-13]
CAD Model/CAD/L connector.SLDPRT
39.0 x 39.0 x 18.0 mm
