basnetsaroj/Batch_distillation_paper/CAD Model/CAD/connectpipe.SLDPRT

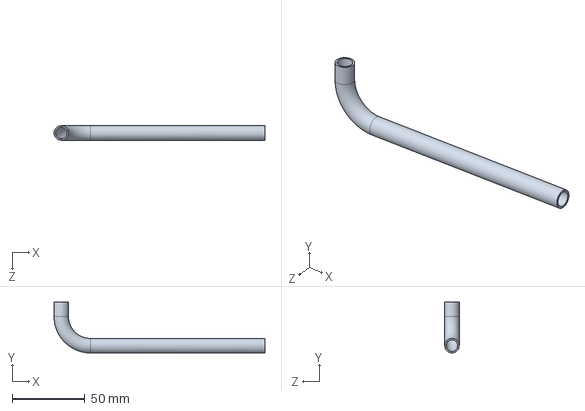
[picture p111: CAD file, 2026-08-13]
CAD Model/CAD/connectpipe.SLDPRT
145.0 x 35.0 x 10.0 mm
