basnetsaroj/Batch_distillation_paper/CAD Model/CAD/in pipe 0.SLDPRT

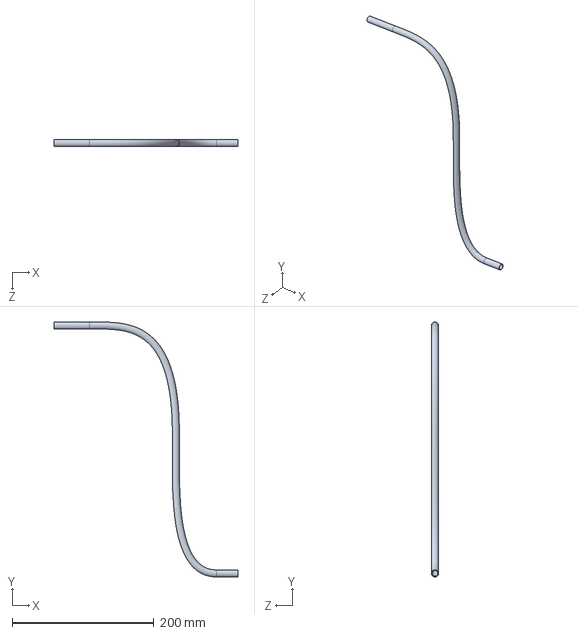
[picture p112: CAD file, 2026-08-13]
CAD Model/CAD/in pipe 0.SLDPRT
259.2 x 360.0 x 10.0 mm
