basnetsaroj/Batch_distillation_paper/CAD Model/CAD/pipe bypass.SLDPRT

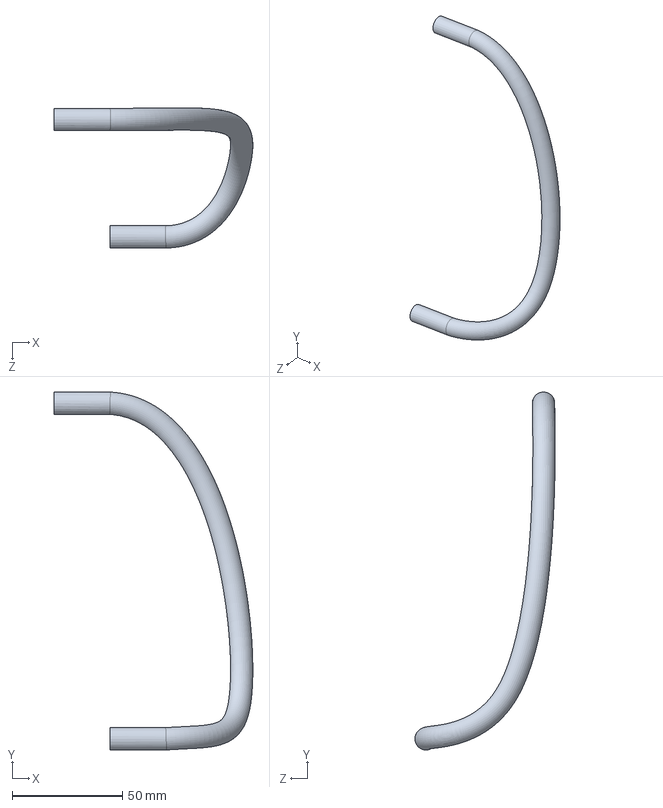
[picture p113: CAD file, 2026-08-13]
CAD Model/CAD/pipe bypass.SLDPRT
90.2 x 162.6 x 63.7 mm
