basnetsaroj/Batch_distillation_paper/CAD Model/CAD/Final assembly 4.SLDASM

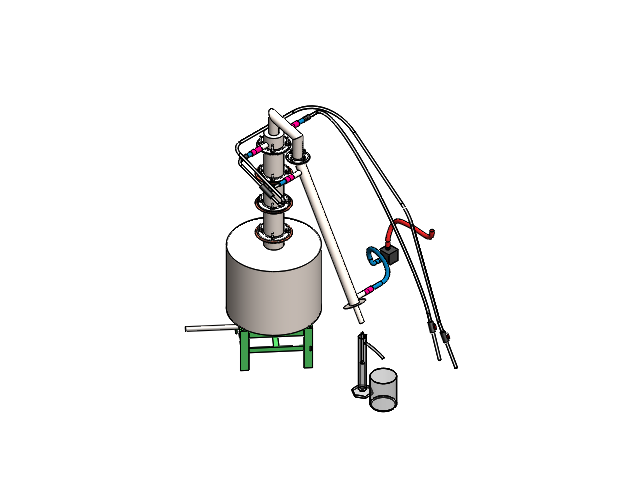
[picture p115: CAD file, 2026-08-13]
CAD Model/CAD/Final assembly 4.SLDASM
base new
column x 3
in pipe
out pipe
water motor
condenser 2
gasket 2 x 7
gasket 3 x 7
Tray x 3
internal x 6
downcomer x 3
bubble cap x 9
countersunk raised head cross recess screw_iso x 6
hex thin nut chamfered gradeab_iso x 6
plain washer large grade ac_iso x 6
curve top
T pipe
connection
connection 2 x 2
gasket condenser
gasket condenser 2nd
connectpipe
connector x 2
stove
out pipe 4
Ball valve x 2
connectpipe 1 x 2
tube
alcoholmeter
hex bolt gradeab_iso x 16
hex nut gradec_iso x 20
plain washer 10669 type nl_iso x 40
countersunk flat head cross recess screw_iso x 4
