basnetsaroj/Batch_distillation_paper/CAD Model/CAD/Design Photos/Full Assembly.png

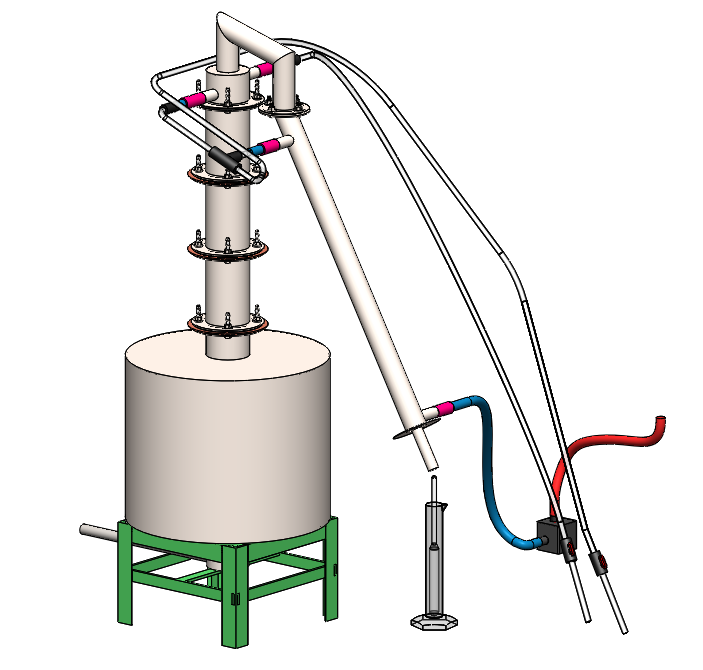
CAD Model/CAD/Design Photos/Full Assembly.png
