basnetsaroj/Batch_distillation_paper/CAD Model/CAD/Design Photos/SAssembly.png

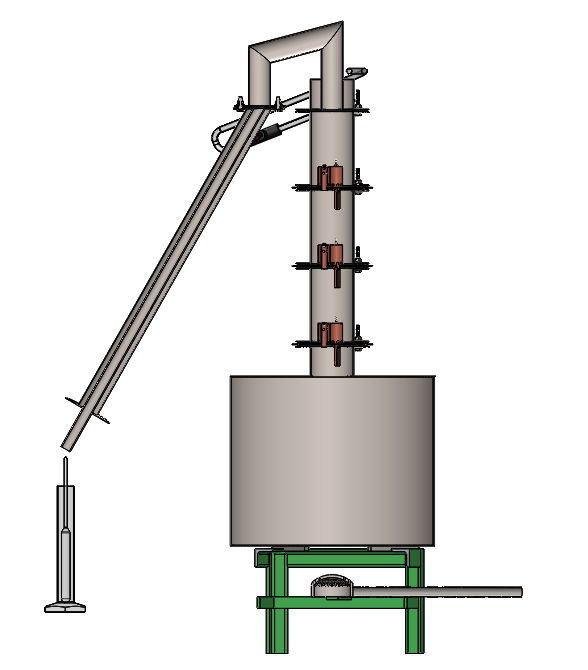
CAD Model/CAD/Design Photos/SAssembly.png
