basnetsaroj/Batch_distillation_paper/CAD Model/CAD/Design Photos/Section tray assembly.PNG

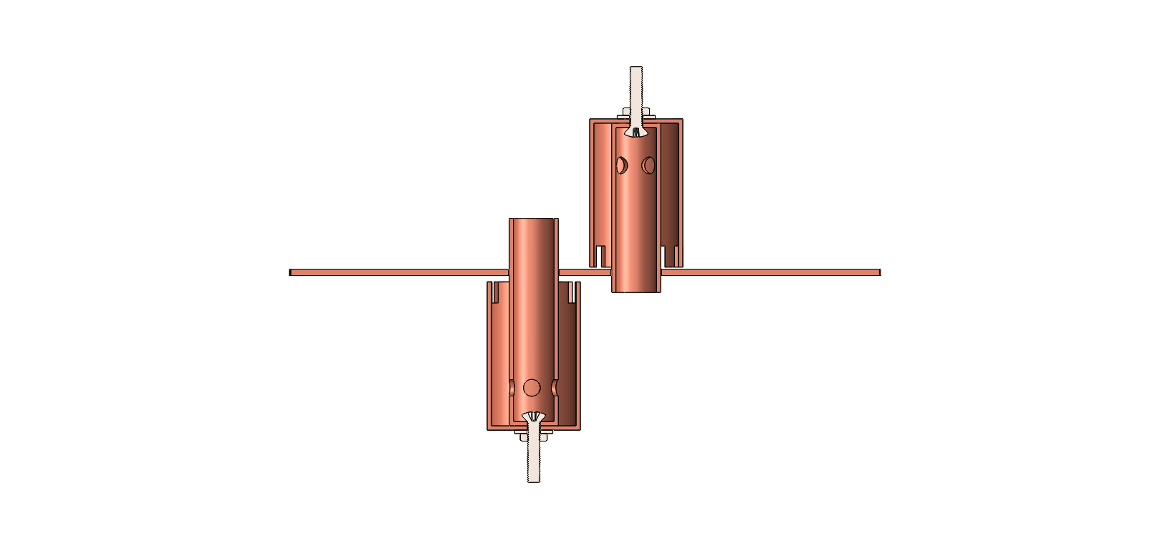
CAD Model/CAD/Design Photos/Section tray assembly.PNG
