basnetsaroj/Batch_distillation_paper/CAD Model/Traditional/p5 assembled.jpg

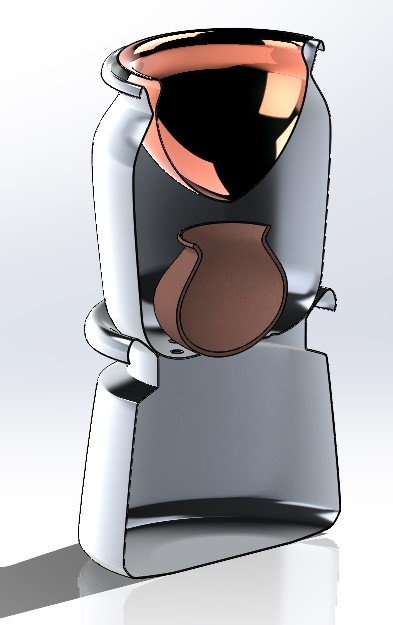
CAD Model/Traditional/p5 assembled.jpg
