basnetsaroj/Batch_distillation_paper/CAD Model/Traditional/photo assembly 2.PNG

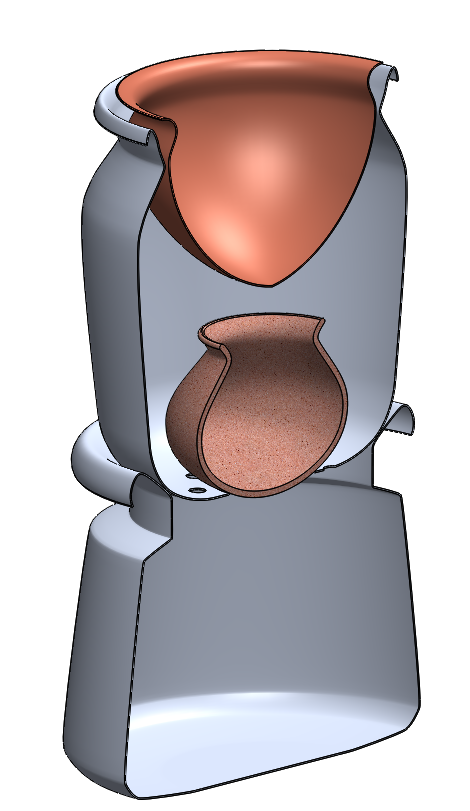
CAD Model/Traditional/photo assembly 2.PNG
