basnetsaroj/Batch_distillation_paper/CAD Model/Traditional/trad assembly ortho.PNG

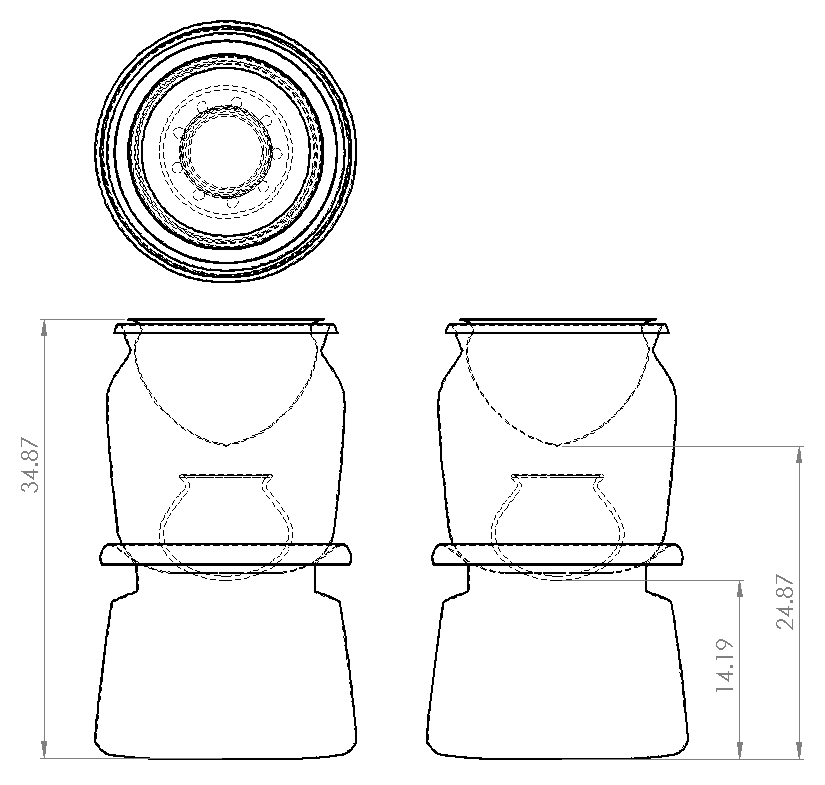
CAD Model/Traditional/trad assembly ortho.PNG
